sbanik1/UHV-Chamber-Designs/6 Way Cross Setup/6 way cross setup.SLDASM

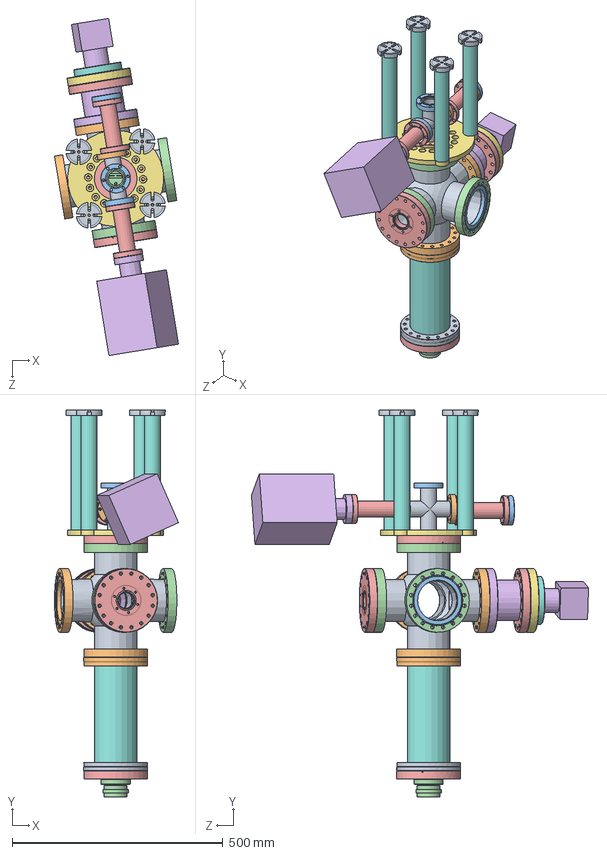
[picture p22: CAD file, 2020-12-12]
6 Way Cross Setup/6 way cross setup.SLDASM
294.7 x 919.1 x 800.7 mm
110026 (6.0 X 4.0 NR) x 3
100026 (6.0 X 4.0 INS) x 3
100026 (6.0 X 4.0 REC) x 3
6WayPump outer
6WayPump inner
6WayPump conflat
405002 P1_405002-001 x 2
405002 P2_110014 (2.75 X 1.5 NR)_1 x 2
405002 P4_100014 (2.75 X 1.5 REC)_1 x 2
405002 P5_100014 (2.75 X 1.5 INS)_1 x 2
402002 rev A x 2
RGAevision2
Washer 6 Way Cross
P0001632
P0000235
P0000448
P0000507
Varian Tisub
NexTorr Nipple P1_110025 modified
NexTorr Nipple P2_110025 modified
NexTorr Nipple Reducer_150018
Damped Post for 6 way cross P1 x 4
Damped Post for 6 way cross P3_PB2 x 4
Damped Post for 6 way cross P2_90322A235 x 8
Ion Gauge conflat_110008_1
Ion Gauge Inner Filaments
