sbanik1/UHV-Chamber-Designs/Main Chamber/Bucket Window/Bucket Window.SLDASM

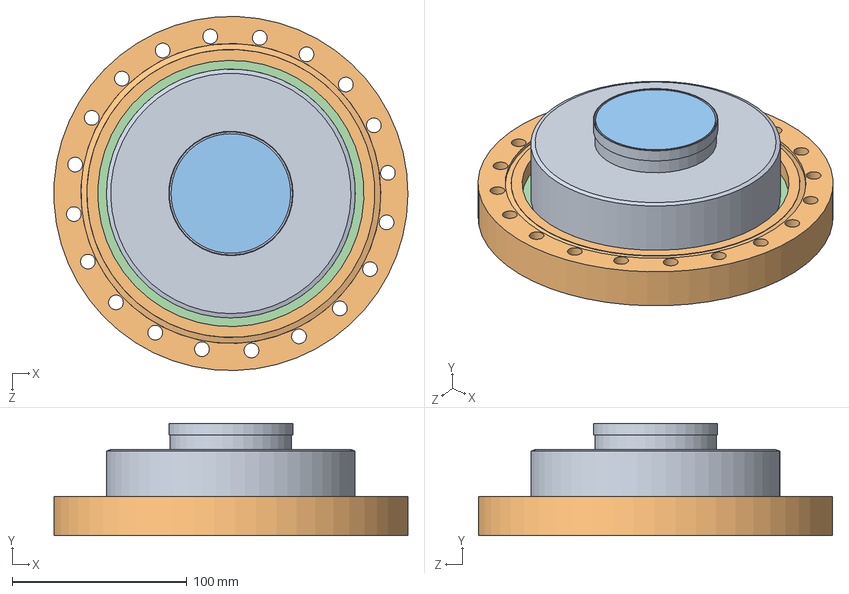
[picture p23: CAD file, 2020-12-12]
Main Chamber/Bucket Window/Bucket Window.SLDASM
202.3 x 64.0 x 202.3 mm
ISAdaptor
ISFlange
ISWindow
RecessedRing
