sbanik1/UHV-Chamber-Designs/Main Chamber/Mini lens stack holder/1.33 Viewport/1.33 Viewport.SLDASM

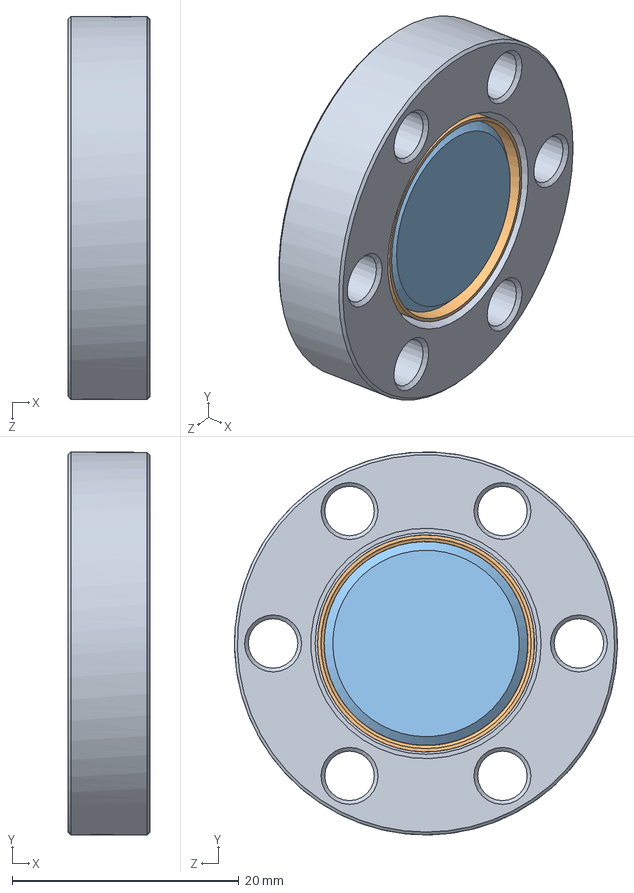
[picture p24: CAD file, 2020-12-12]
Main Chamber/Mini lens stack holder/1.33 Viewport/1.33 Viewport.SLDASM
7.24 x 33.8 x 33.8 mm
0784101L
0194307B
1002201A
