sbanik1/UHV-Chamber-Designs/2D MOT/Conical Adapter 1.33-2.75/Conical Adapter 1.33-2.75.SLDASM

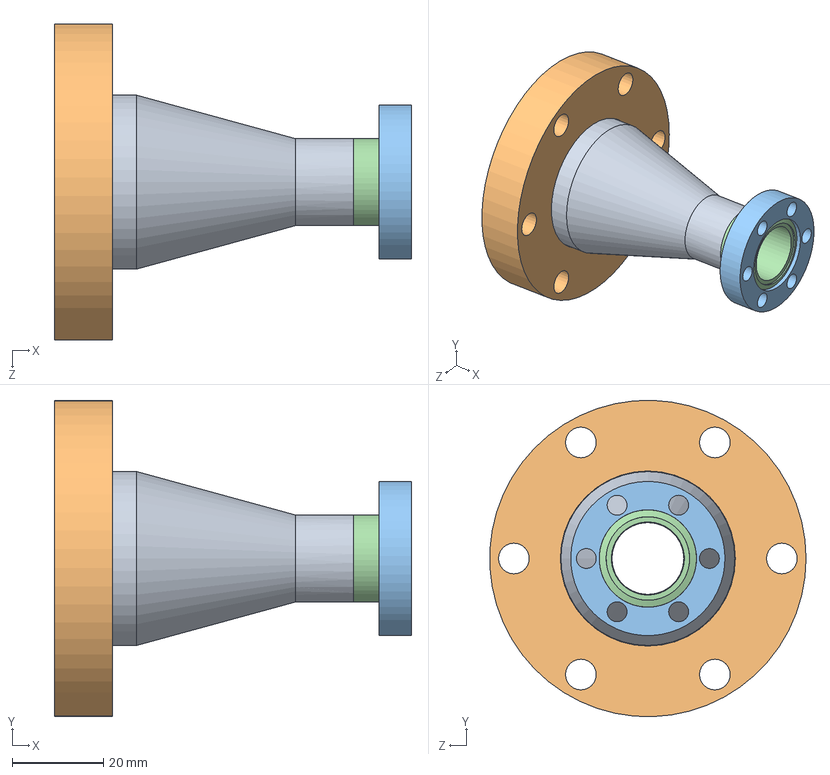
[picture p25: CAD file, 2020-12-12]
2D MOT/Conical Adapter 1.33-2.75/Conical Adapter 1.33-2.75.SLDASM
78.2 x 69.3 x 69.3 mm
110014 (2.75 X 1.5 NR)
100004 (1.33 X .75 REC)
100004 (1.33 X .75 INS)
