sbanik1/UHV-Chamber-Designs/2D MOT/Tenway Cross/Second Species Assembly.SLDASM

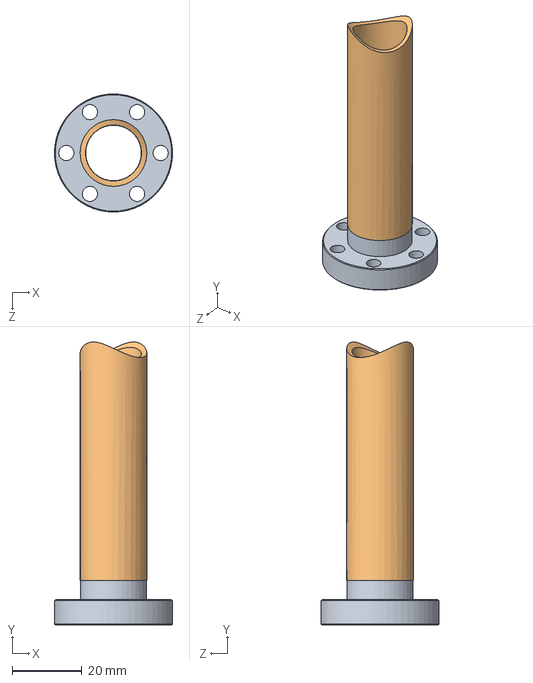
[picture p26: CAD file, 2020-12-12]
2D MOT/Tenway Cross/Second Species Assembly.SLDASM
33.8 x 80.9 x 33.8 mm
MiniFlange-weld-mine
OvenTube
