sbanik1/UHV-Chamber-Designs/6 Way Cross Setup/Damped posts/Damped Post for 6 way cross.SLDASM

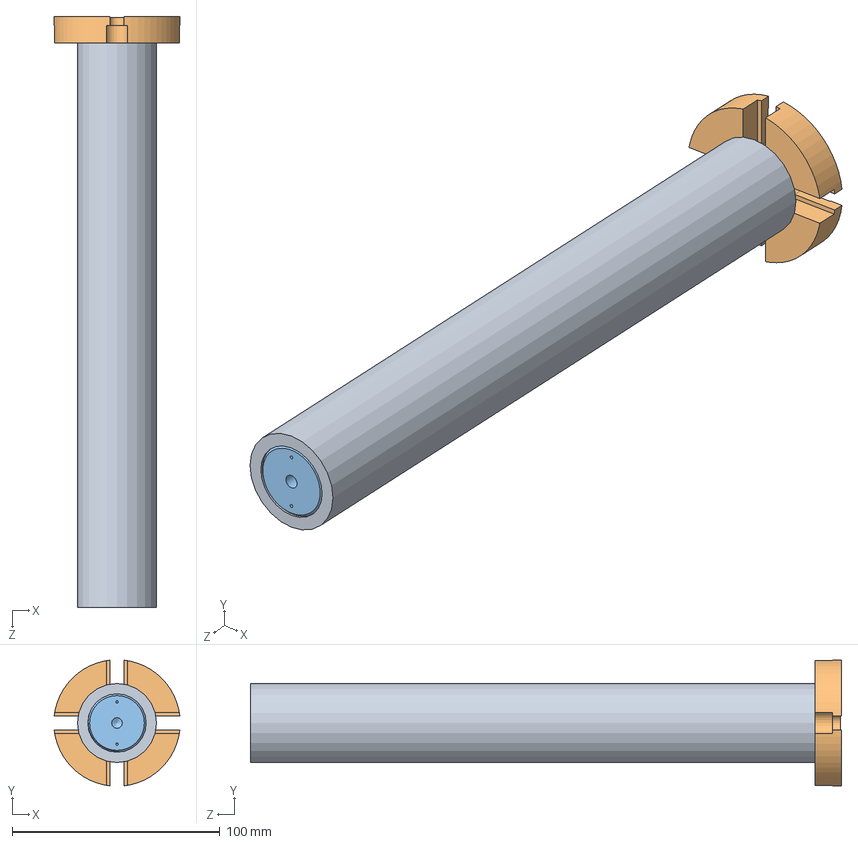
[picture p27: CAD file, 2020-12-12]
6 Way Cross Setup/Damped posts/Damped Post for 6 way cross.SLDASM
60.6 x 60.6 x 284.8 mm
Damped Post for 6 way cross P1
Damped Post for 6 way cross P3_PB2
Damped Post for 6 way cross P2_90322A235 x 2
