sbanik1/UHV-Chamber-Designs/Main Chamber/Damped Post Main Chamber/Damped Post for Main Chamber Bottom.SLDASM

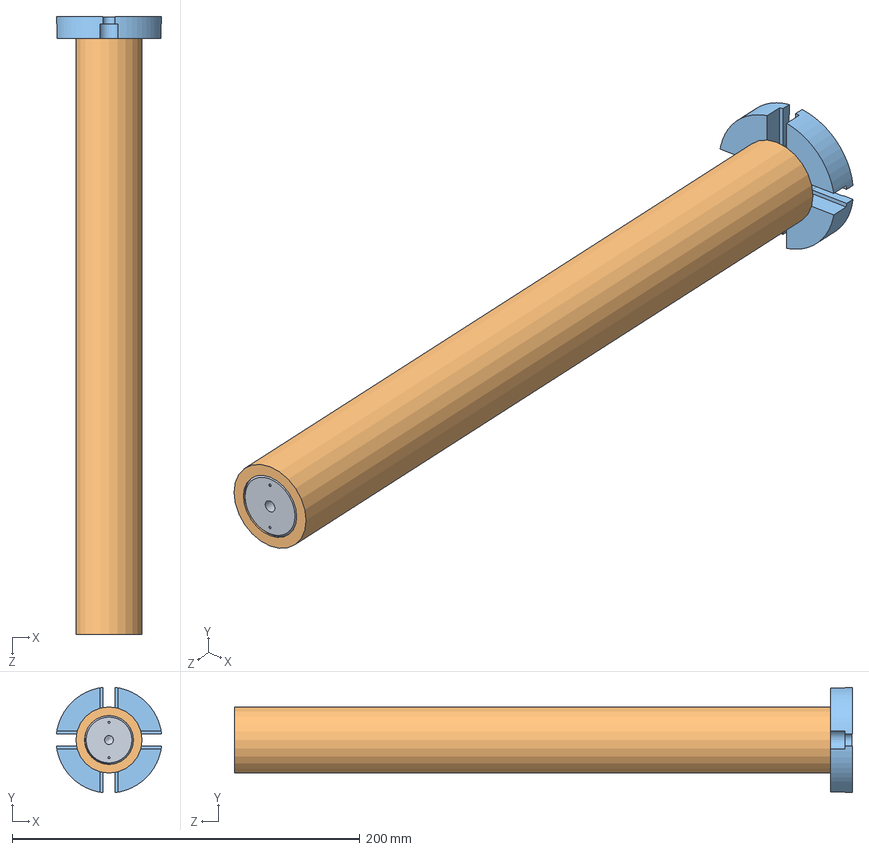
[picture p28: CAD file, 2020-12-12]
Main Chamber/Damped Post Main Chamber/Damped Post for Main Chamber Bottom.SLDASM
60.6 x 60.6 x 355.6 mm
Damped Post for Main Chamber P2_90322A235 x 2
Damped Post for Main Chamber Bottom P1
Damped Post for Main Chamber P3_PB2
