sbanik1/UHV-Chamber-Designs/2D MOT/Erbium Source/Er Source P1.SLDASM

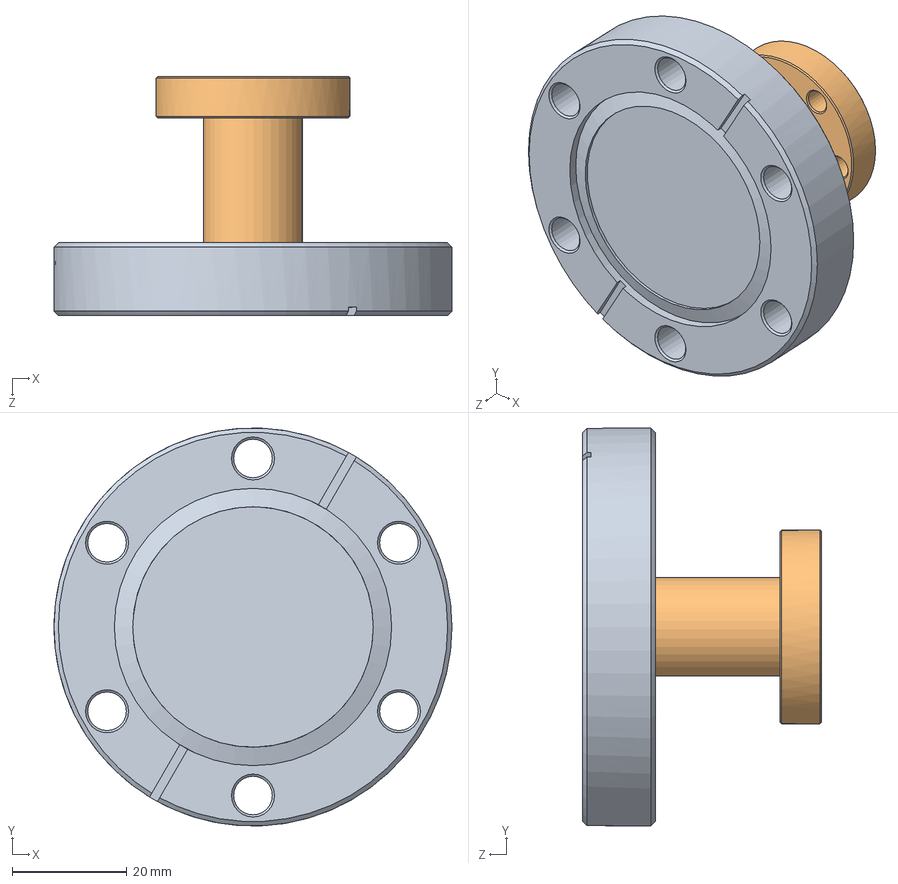
[picture p29: CAD file, 2020-12-12]
2D MOT/Erbium Source/Er Source P1.SLDASM
69.3 x 69.3 x 41.7 mm
Er Source P1-2_110008
Er Source P1-1_110002
