sbanik1/UHV-Chamber-Designs/6 Way Cross Setup/Ion Gauge/Ion Gauge.SLDASM

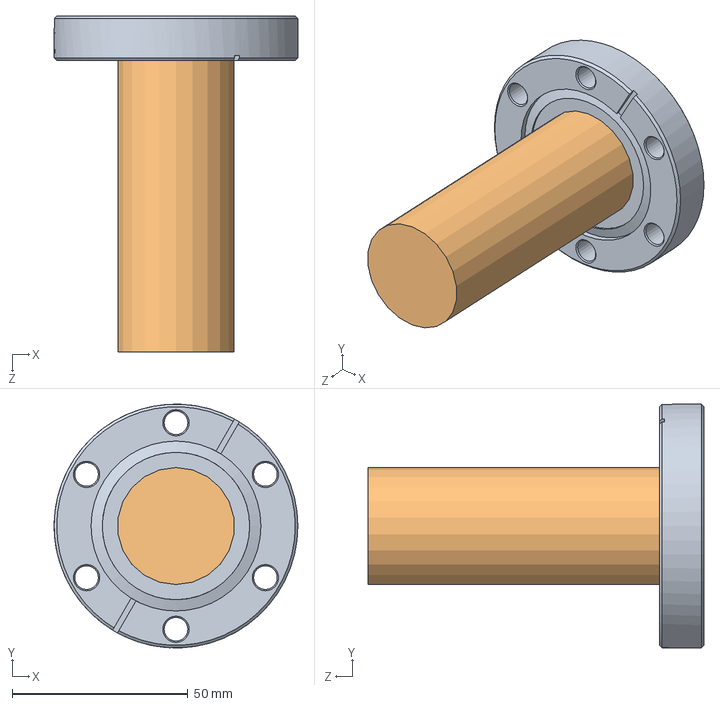
[picture p30: CAD file, 2020-12-12]
6 Way Cross Setup/Ion Gauge/Ion Gauge.SLDASM
69.3 x 69.3 x 95.6 mm
Ion Gauge conflat_110008_1
Ion Gauge Inner Filaments
