sbanik1/UHV-Chamber-Designs/6 Way Cross Setup/NextTorr Nipple/NexTorr Nipple.SLDASM

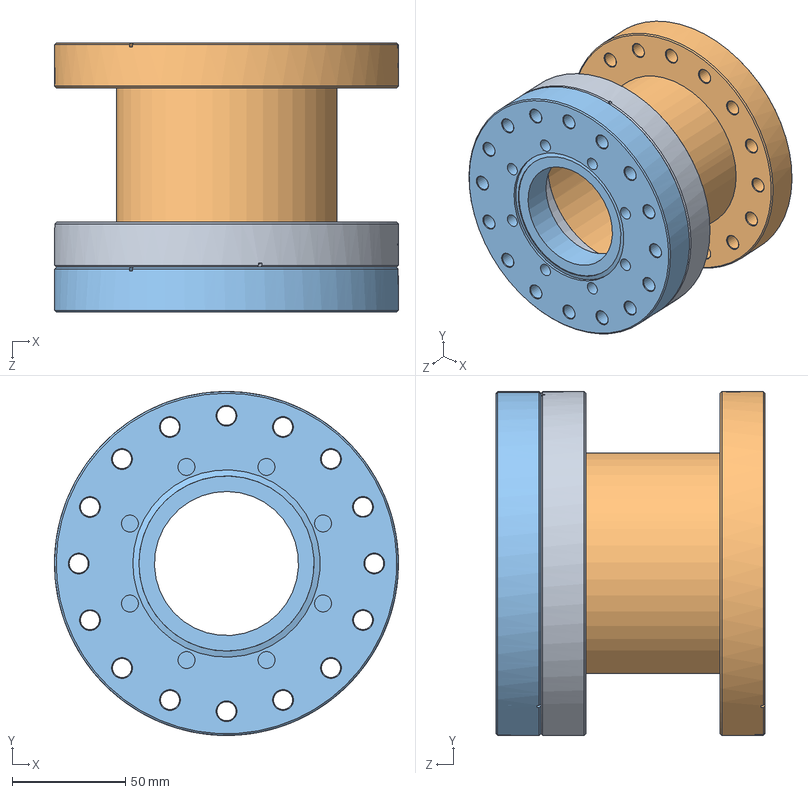
[picture p31: CAD file, 2020-12-12]
6 Way Cross Setup/NextTorr Nipple/NexTorr Nipple.SLDASM
151.6 x 151.6 x 118.6 mm
NexTorr Nipple P1_110025 modified
NexTorr Nipple P2_110025 modified
NexTorr Nipple Reducer_150018
