sbanik1/UHV-Chamber-Designs/6 Way Cross Setup/TSP Nipple/TSP nipple_fn-0600.SLDASM

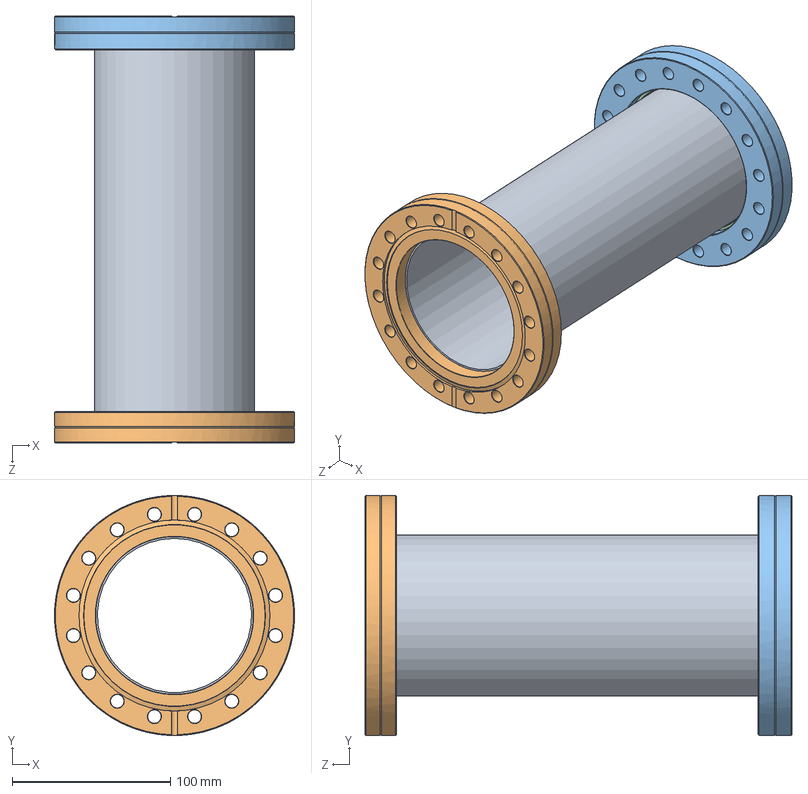
[picture p32: CAD file, 2020-12-12]
6 Way Cross Setup/TSP Nipple/TSP nipple_fn-0600.SLDASM
151.6 x 151.6 x 269.7 mm
P0001632
P0000235
P0000448
P0000507
