sbanik1/UHV-Chamber-Designs/Main Chamber/4.5 VP Assembly/4.5 Viewport/Viewport 4.5_9722007.SLDASM

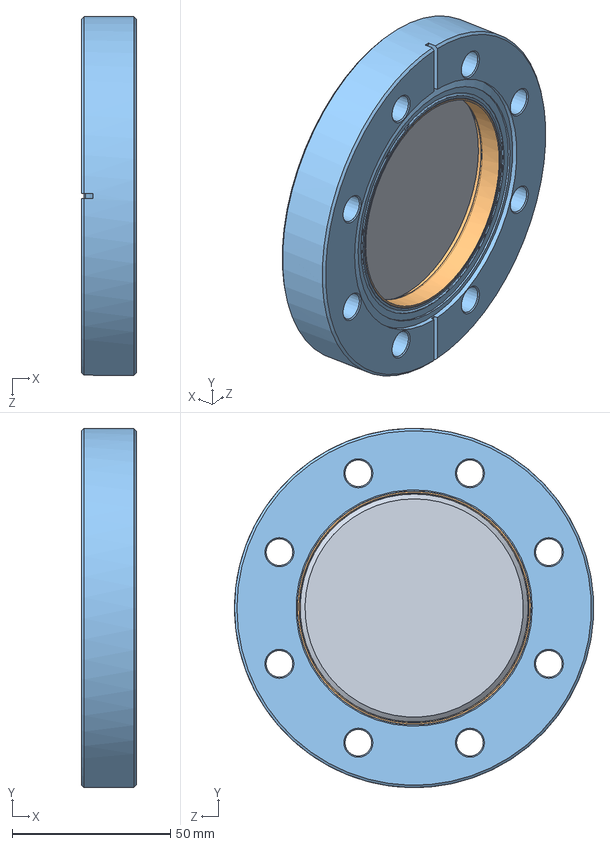
[picture p33: CAD file, 2020-12-12]
Main Chamber/4.5 VP Assembly/4.5 Viewport/Viewport 4.5_9722007.SLDASM
17.3 x 113.5 x 113.4 mm
1002203A
Viewport 4.5 P1_0194302B
Viewport 4.5 P2_0194603B
