sbanik1/UHV-Chamber-Designs/Main Chamber/Damped Post Main Chamber/Damped Post for Main Chamber Bottom P1.SLDPRT

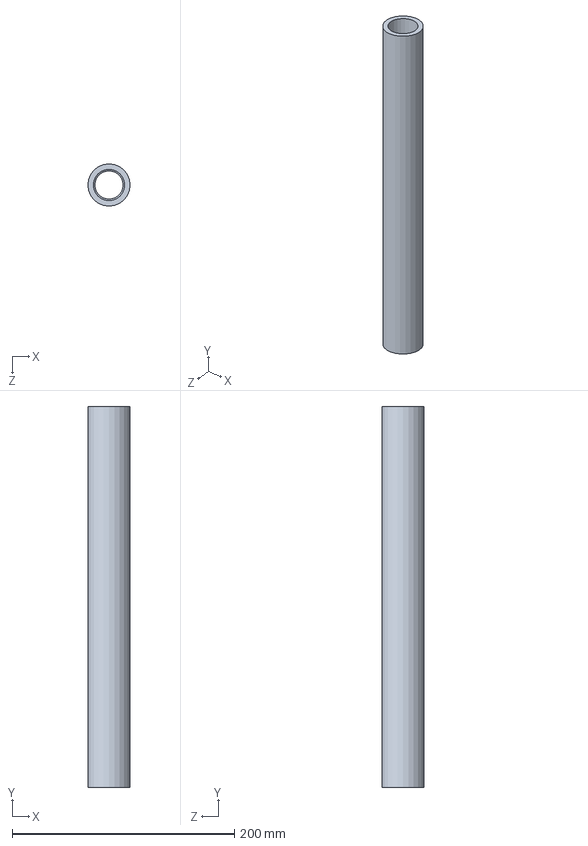
[picture p34: CAD file, 2020-12-12]
Main Chamber/Damped Post Main Chamber/Damped Post for Main Chamber Bottom P1.SLDPRT
38.1 x 342.9 x 38.1 mm
