sbanik1/UHV-Chamber-Designs/2D MOT/2.75 Four Way Cross/2.75 Four Way Cross.SLDASM

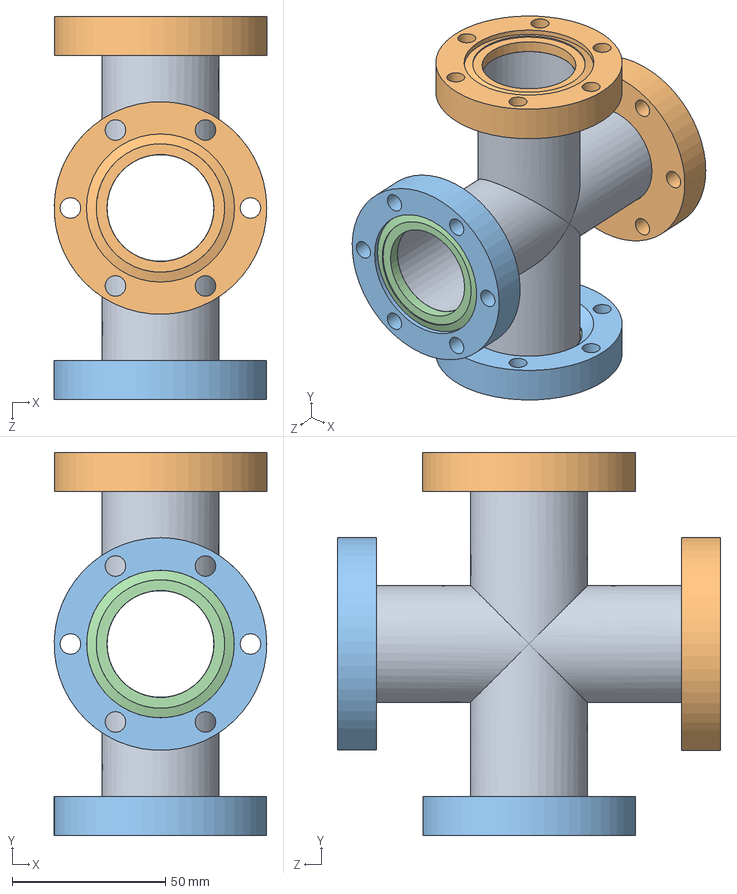
[picture p35: CAD file, 2020-12-12]
2D MOT/2.75 Four Way Cross/2.75 Four Way Cross.SLDASM
69.3 x 124.9 x 124.9 mm
405002 P1_405002-001 x 2
405002 P2_110014 (2.75 X 1.5 NR)_1 x 2
405002 P4_100014 (2.75 X 1.5 REC)_1 x 2
405002 P5_100014 (2.75 X 1.5 INS)_1 x 2
