sbanik1/UHV-Chamber-Designs/2D MOT/2.75 Window/2.75 Window.SLDASM

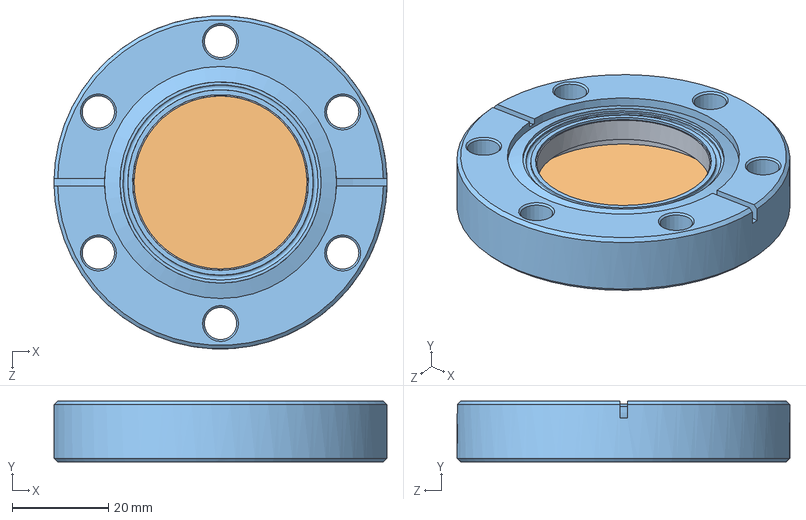
[picture p36: CAD file, 2020-12-12]
2D MOT/2.75 Window/2.75 Window.SLDASM
69.3 x 12.7 x 69.3 mm
2.75 Window P1-1
2.75 Window P1-2
2.75 Window P2
