sbanik1/UHV-Chamber-Designs/Main Chamber/Damped Post Main Chamber/Damped Post for Main Chamber P2_90322A235.SLDPRT

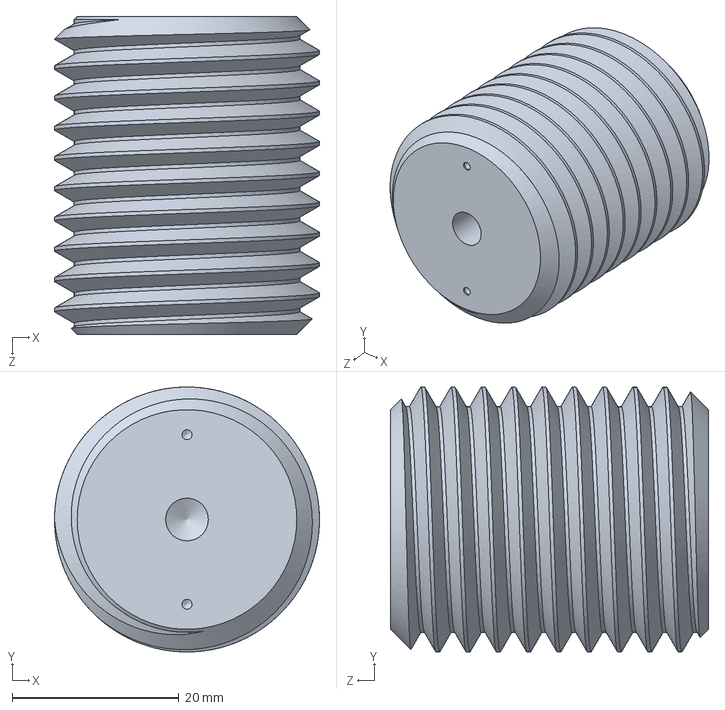
[picture p37: CAD file, 2020-12-12]
Main Chamber/Damped Post Main Chamber/Damped Post for Main Chamber P2_90322A235.SLDPRT
31.7 x 31.7 x 38.1 mm
