sbanik1/UHV-Chamber-Designs/2D MOT/Tenway Cross/Chamber Tube Assembly.SLDASM

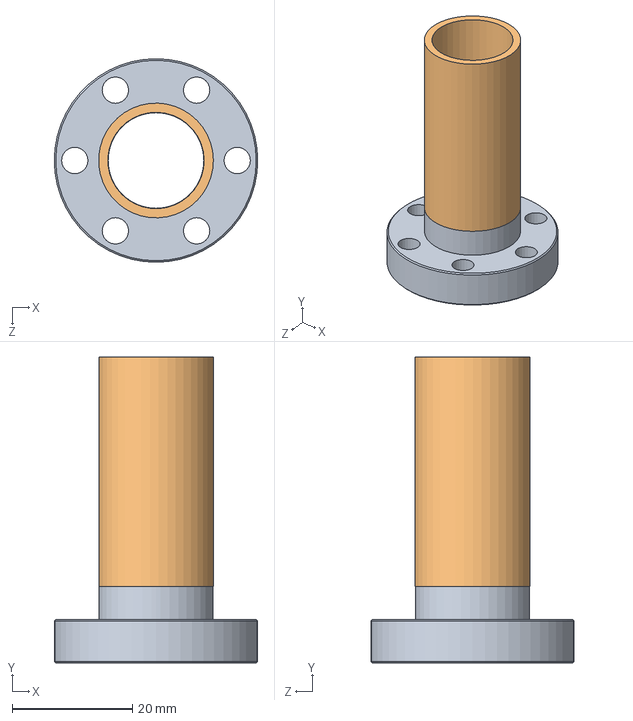
[picture p38: CAD file, 2020-12-12]
2D MOT/Tenway Cross/Chamber Tube Assembly.SLDASM
33.8 x 50.8 x 33.8 mm
MiniFlange-weld-mine
ChamberTube
