sbanik1/UHV-Chamber-Designs/Main Chamber/Damped Post Main Chamber/Damped Post for Main Chamber P3_PB2.sldprt

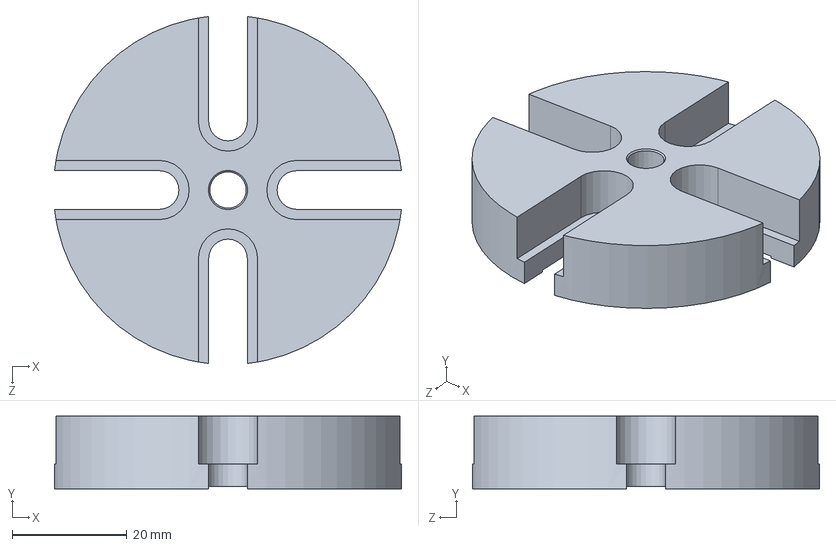
[picture p39: CAD file, 2020-12-12]
Main Chamber/Damped Post Main Chamber/Damped Post for Main Chamber P3_PB2.sldprt
60.6 x 12.7 x 60.6 mm
