sbanik1/UHV-Chamber-Designs/2D MOT/2.75 Window/2.75 Window P1.SLDASM

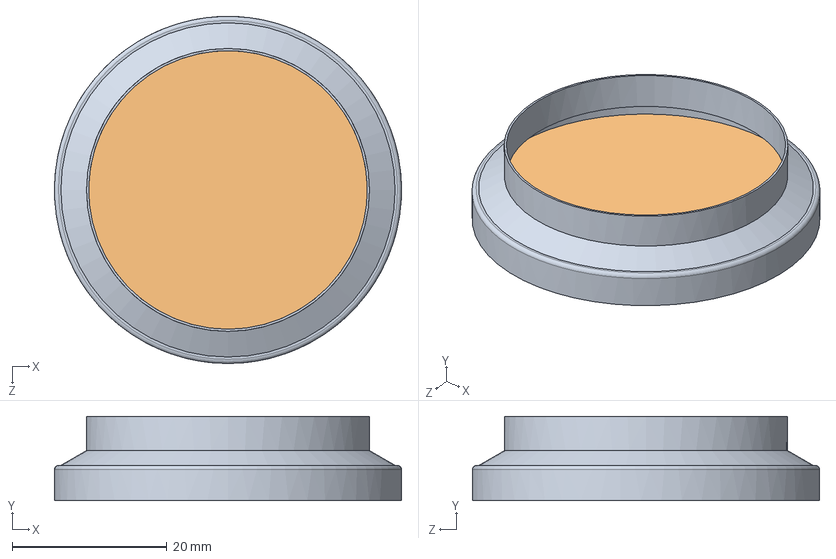
[picture p40: CAD file, 2020-12-12]
2D MOT/2.75 Window/2.75 Window P1.SLDASM
44.9 x 10.9 x 44.9 mm
2.75 Window P1-1
2.75 Window P1-2
