sbanik1/UHV-Chamber-Designs/2D MOT/Erbium Source/Er Source.SLDASM

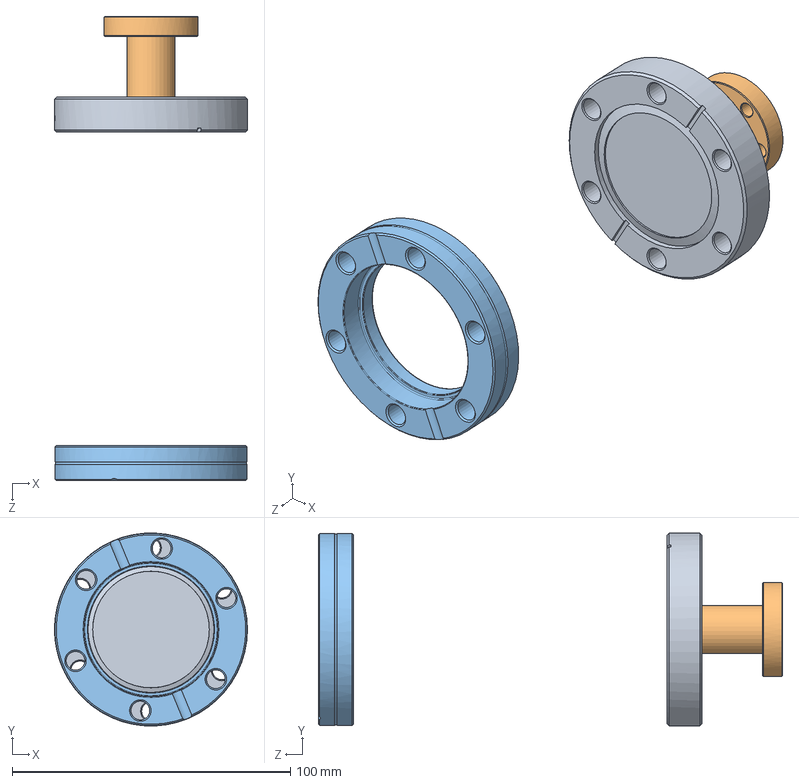
[picture p41: CAD file, 2020-12-12]
2D MOT/Erbium Source/Er Source.SLDASM
69.3 x 69.3 x 166.9 mm
Er Source P1-2_110008
Er Source P1-1_110002
Er Source P2-1-1_P0000436
