sbanik1/UHV-Chamber-Designs/Main Chamber/Damped Post Main Chamber/Damped Post Main Chamber_DP14A.sldprt

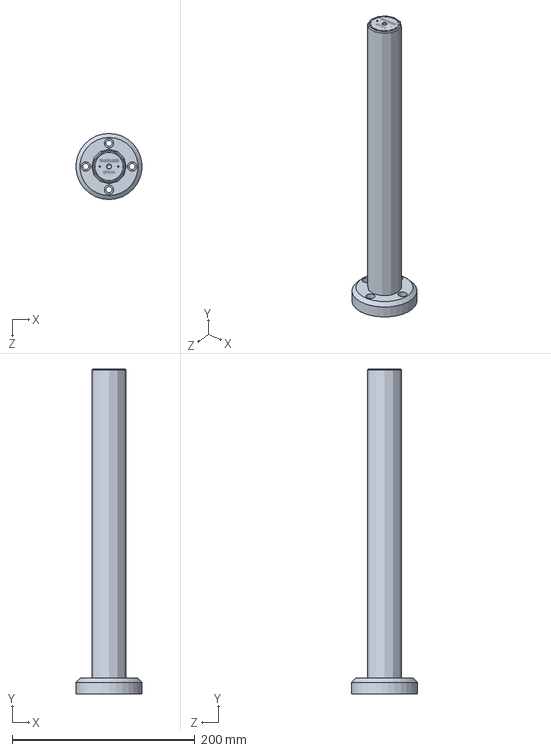
[picture p42: CAD file, 2020-12-12]
Main Chamber/Damped Post Main Chamber/Damped Post Main Chamber_DP14A.sldprt
72.0 x 355.6 x 72.4 mm
