sbanik1/UHV-Chamber-Designs/2D MOT/Tenway Cross/TenwayCross.SLDASM

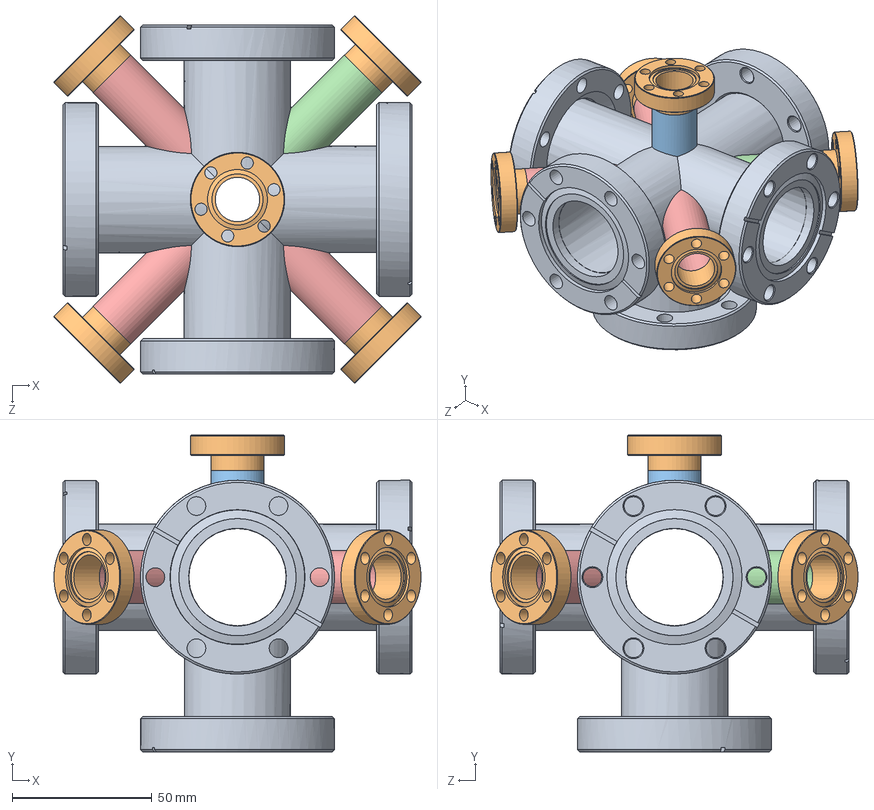
[picture p43: CAD file, 2020-12-12]
2D MOT/Tenway Cross/TenwayCross.SLDASM
131.3 x 113.3 x 131.3 mm
5way MDC-406002-mine
MiniFlange-weld-mine x 5
ChamberTube
CameraTube
OvenTube x 3
