sbanik1/UHV-Chamber-Designs/2D MOT/2.75 Nipple_402002 rev A/2D MOT nipple_402002 rev A.SLDPRT

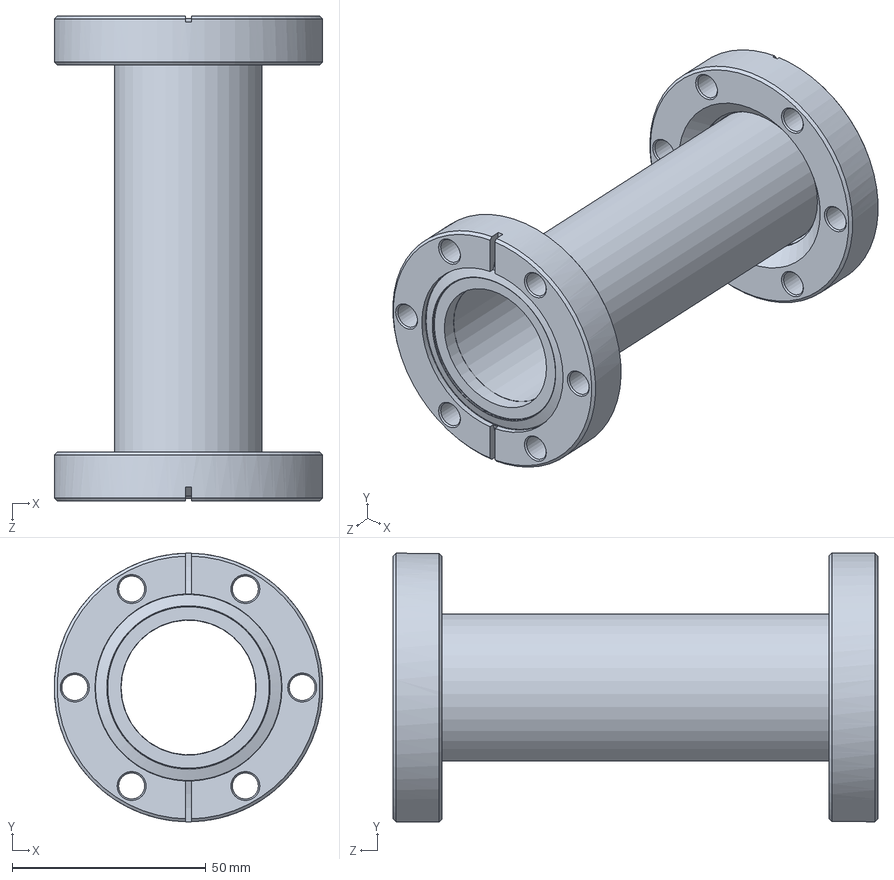
[picture p44: CAD file, 2020-12-12]
2D MOT/2.75 Nipple_402002 rev A/2D MOT nipple_402002 rev A.SLDPRT
69.3 x 69.3 x 125.2 mm
