sbanik1/UHV-Chamber-Designs/2D MOT/2DMOT Bias Coils/Coil mount.SLDPRT

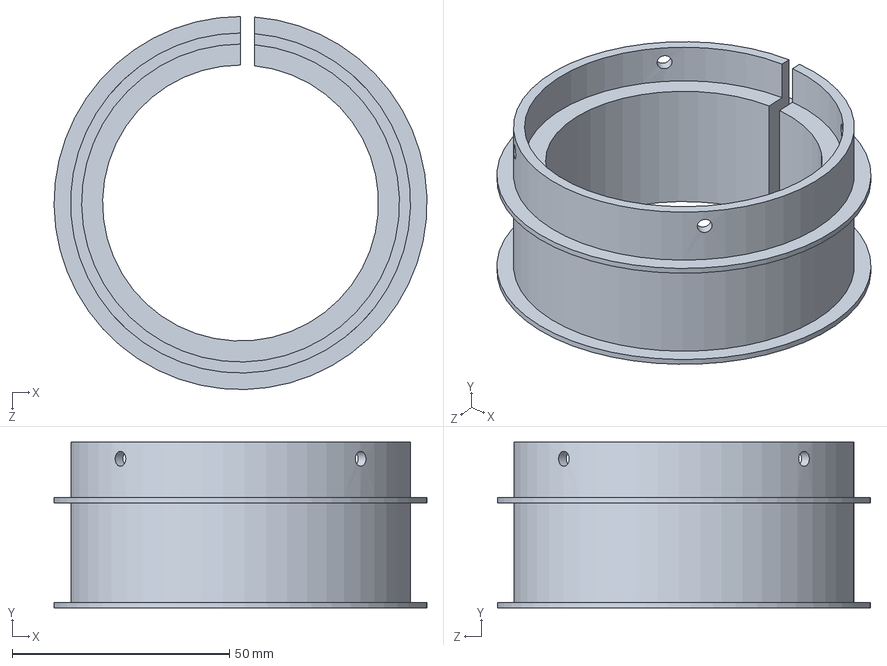
[picture p45: CAD file, 2020-12-12]
2D MOT/2DMOT Bias Coils/Coil mount.SLDPRT
85.8 x 38.1 x 85.8 mm
