sbanik1/UHV-Chamber-Designs/2D MOT/Angle Valve/Angle Valve_314003.SLDPRT

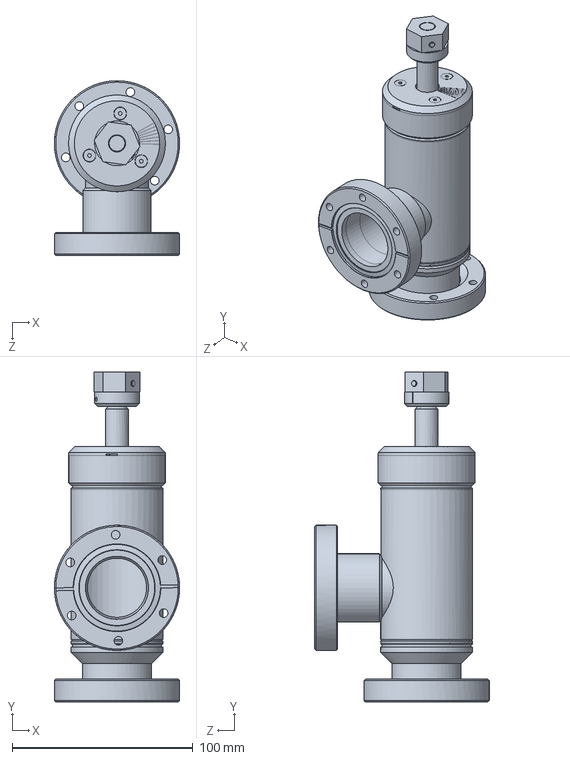
[picture p46: CAD file, 2020-12-12]
2D MOT/Angle Valve/Angle Valve_314003.SLDPRT
69.3 x 182.7 x 96.6 mm
