sbanik1/UHV-Chamber-Designs/2D MOT/Differential Pumping Tube/DiffPumpTube.SLDPRT

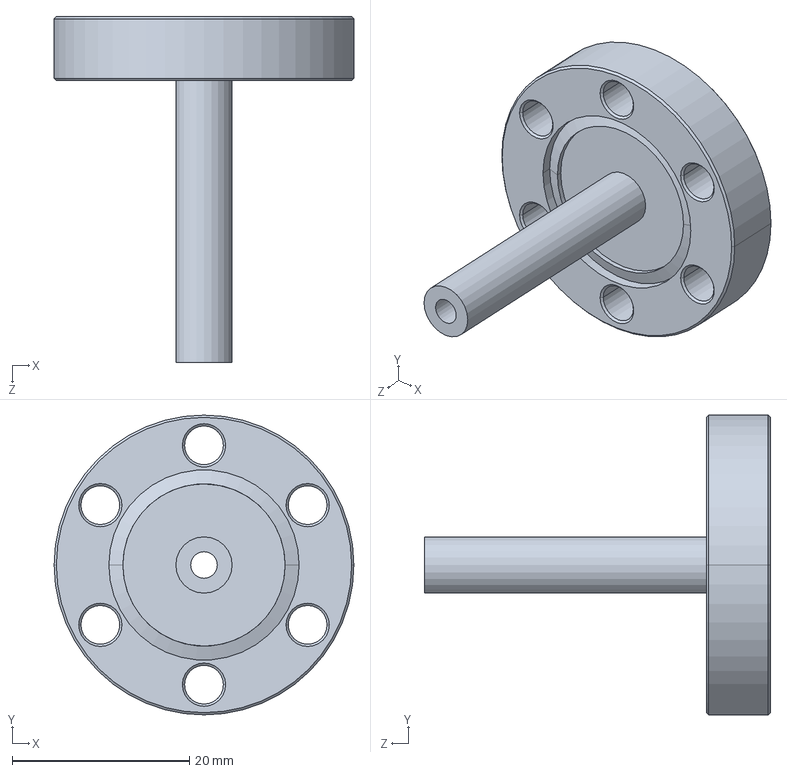
[picture p48: CAD file, 2021-06-03]
2D MOT/Differential Pumping Tube/DiffPumpTube.SLDPRT
33.8 x 33.8 x 39.0 mm
