sbanik1/UHV-Chamber-Designs/2D MOT/Gate Valve/Gate Valve 302000.SLDPRT

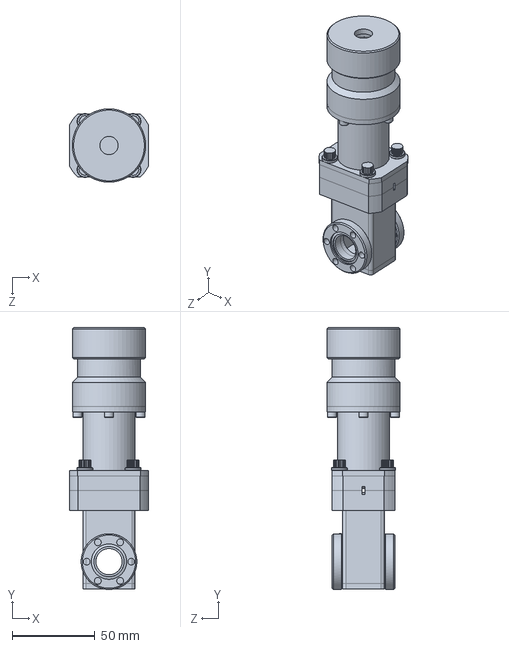
[picture p49: CAD file, 2020-12-12]
2D MOT/Gate Valve/Gate Valve 302000.SLDPRT
47.6 x 158.8 x 44.5 mm
