sbanik1/UHV-Chamber-Designs/6 Way Cross Setup/6 Way Cross Getter SAES D-500/6WayPump conflat.SLDPRT

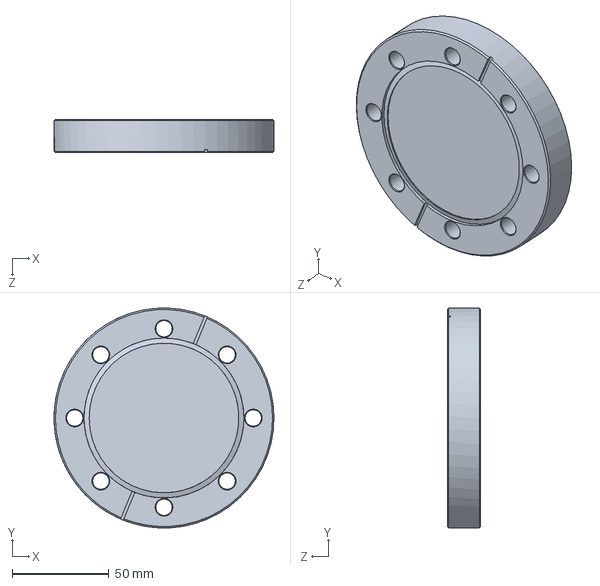
[picture p50: CAD file, 2020-12-12]
6 Way Cross Setup/6 Way Cross Getter SAES D-500/6WayPump conflat.SLDPRT
113.5 x 113.5 x 17.3 mm
