sbanik1/UHV-Chamber-Designs/6 Way Cross Setup/Baffle.SLDPRT

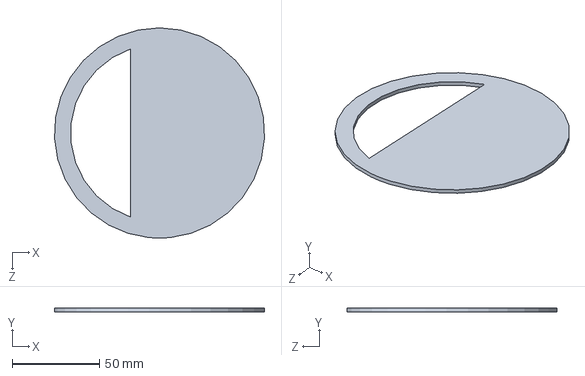
[picture p51: CAD file, 2020-12-12]
6 Way Cross Setup/Baffle.SLDPRT
120.2 x 2.03 x 120.4 mm
