sbanik1/UHV-Chamber-Designs/6 Way Cross Setup/Ion Gauge/Ion Gauge conflat_110008_1.SLDPRT

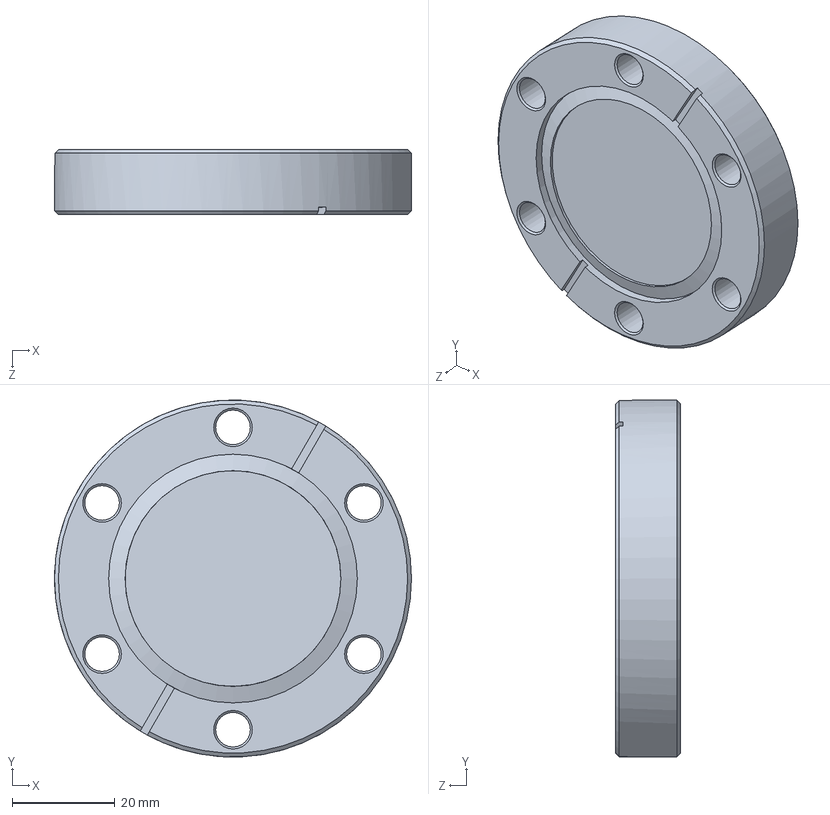
[picture p52: CAD file, 2020-12-12]
6 Way Cross Setup/Ion Gauge/Ion Gauge conflat_110008_1.SLDPRT
69.3 x 69.3 x 12.7 mm
