sbanik1/UHV-Chamber-Designs/6 Way Cross Setup/RGA/RGAevision2.SLDPRT

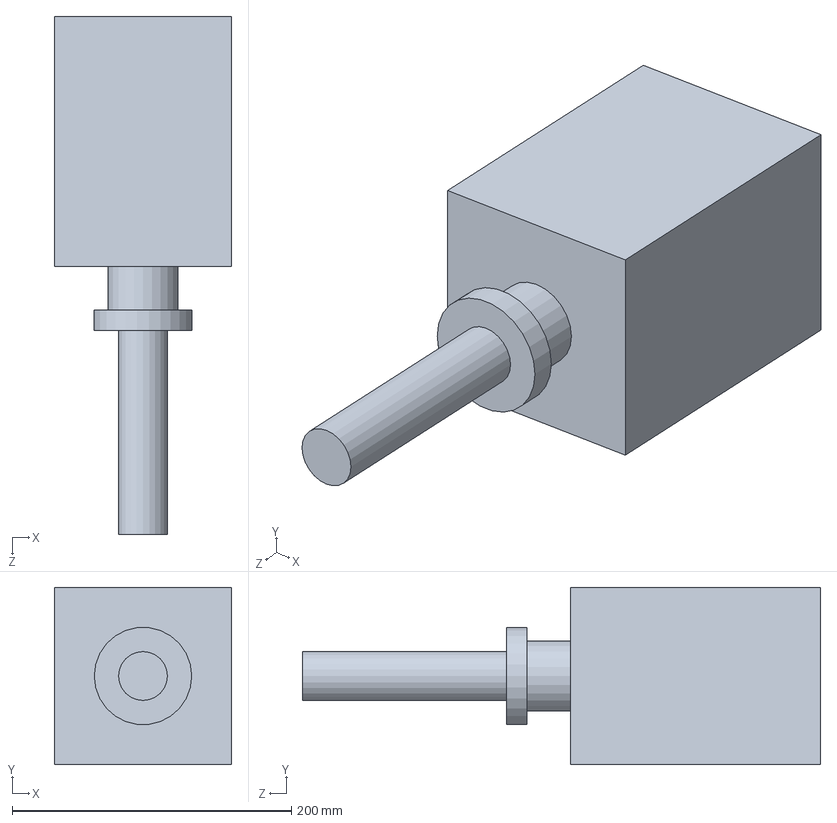
[picture p54: CAD file, 2020-12-12]
6 Way Cross Setup/RGA/RGAevision2.SLDPRT
127.0 x 127.0 x 371.1 mm
