sbanik1/UHV-Chamber-Designs/6 Way Cross Setup/Ti Sub/Varian Tisub.SLDPRT

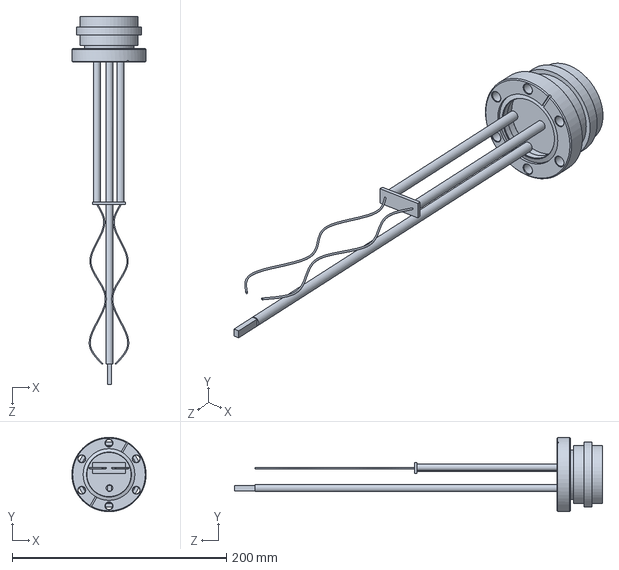
[picture p55: CAD file, 2020-12-12]
6 Way Cross Setup/Ti Sub/Varian Tisub.SLDPRT
69.3 x 69.3 x 343.6 mm
