sbanik1/UHV-Chamber-Designs/Main Chamber/Bucket Window/RecessedRing.SLDPRT

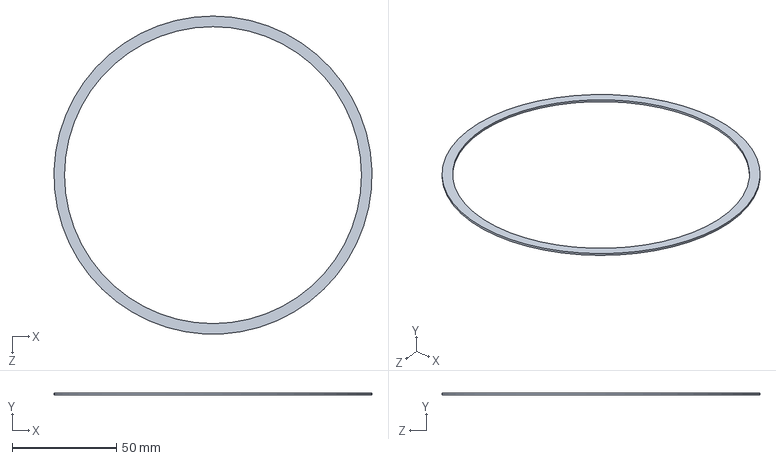
[picture p57: CAD file, 2020-12-12]
Main Chamber/Bucket Window/RecessedRing.SLDPRT
152.3 x 1 x 152.3 mm
