sbanik1/UHV-Chamber-Designs/Main Chamber/Chamber/Modified Kimball Chamber.SLDPRT

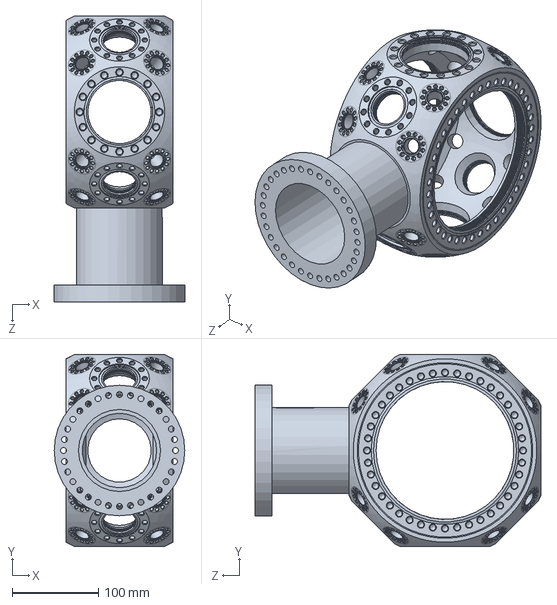
[picture p58: CAD file, 2020-12-12]
Main Chamber/Chamber/Modified Kimball Chamber.SLDPRT
151.6 x 223.0 x 332.2 mm
