sbanik1/UHV-Chamber-Designs/Optical Table Surface/optical table Surface.SLDPRT

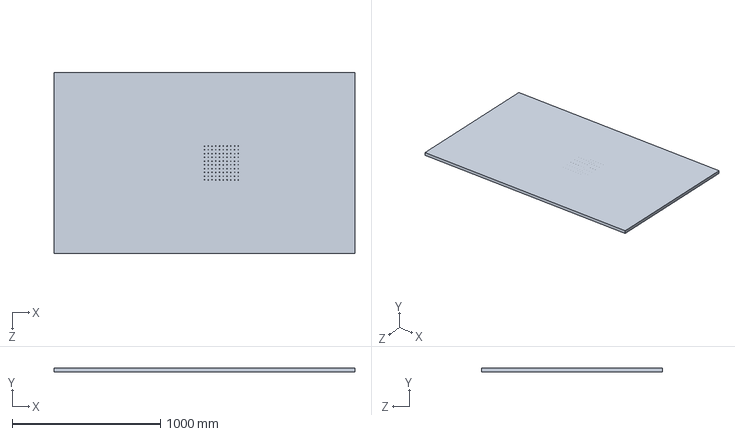
[picture p59: CAD file, 2020-12-12]
Optical Table Surface/optical table Surface.SLDPRT
2032.0 x 25.4 x 1219.2 mm
