sbanik1/UHV-Chamber-Designs/2D MOT/Sodium Oven/Cup.SLDPRT

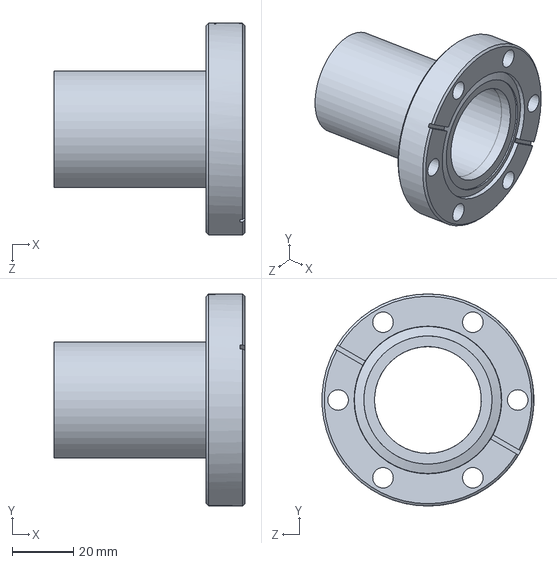
[picture p60: CAD file, 2020-12-12]
2D MOT/Sodium Oven/Cup.SLDPRT
62.5 x 69.3 x 69.3 mm
