sbanik1/UHV-Chamber-Designs/2D MOT/Tenway Cross/5way MDC-406002-mine.SLDPRT

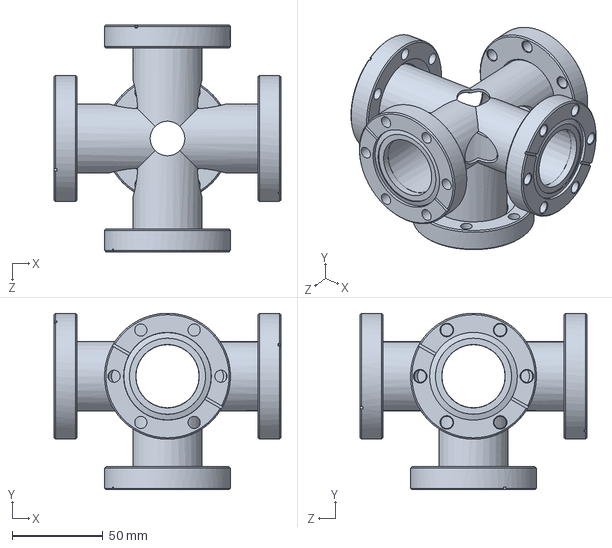
[picture p61: CAD file, 2020-12-12]
2D MOT/Tenway Cross/5way MDC-406002-mine.SLDPRT
125.0 x 97.2 x 125.0 mm
