sbanik1/UHV-Chamber-Designs/6 Way Cross Setup/NextTorr Nipple/NexTorr Nipple P2_110025 modified.SLDPRT

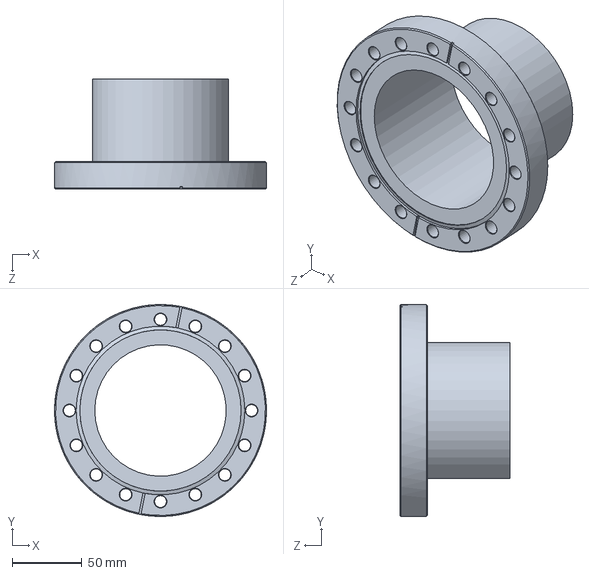
[picture p62: CAD file, 2020-12-12]
6 Way Cross Setup/NextTorr Nipple/NexTorr Nipple P2_110025 modified.SLDPRT
151.6 x 151.6 x 79.0 mm
