sbanik1/UHV-Chamber-Designs/6 Way Cross Setup/Ti Sub/TiSub 2_34CFBlankFlangeClear.SLDPRT

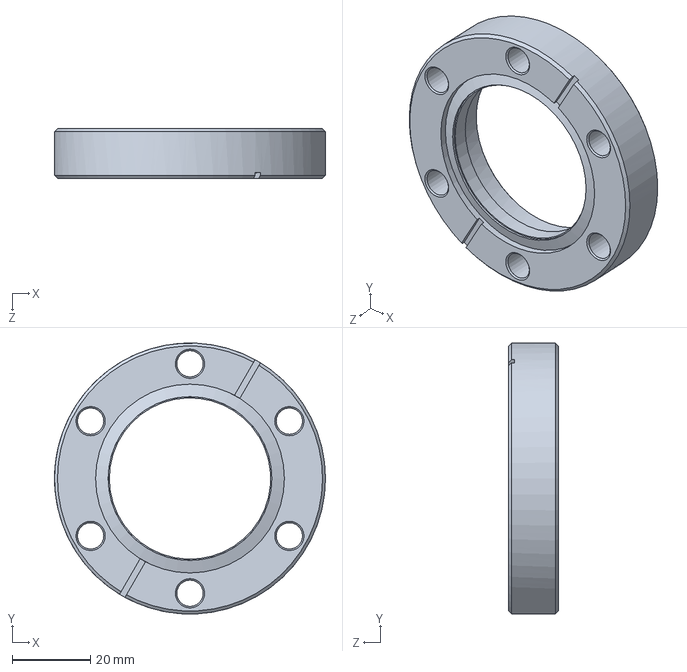
[picture p63: CAD file, 2020-12-12]
6 Way Cross Setup/Ti Sub/TiSub 2_34CFBlankFlangeClear.SLDPRT
69.3 x 69.3 x 12.7 mm
