sbanik1/UHV-Chamber-Designs/Bread Boards/Bread Board Top NO HOLES.SLDPRT

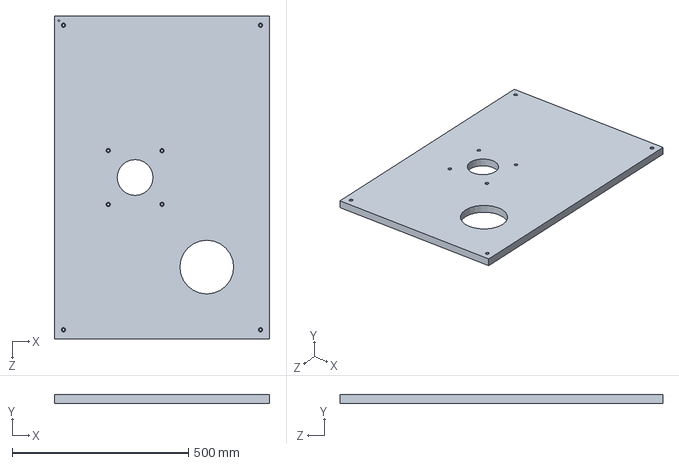
[picture p64: CAD file, 2020-12-12]
Bread Boards/Bread Board Top NO HOLES.SLDPRT
609.6 x 25.4 x 914.4 mm
