sbanik1/UHV-Chamber-Designs/Main Chamber/Damped Post Main Chamber/Chamber Top Post_P6.sldprt

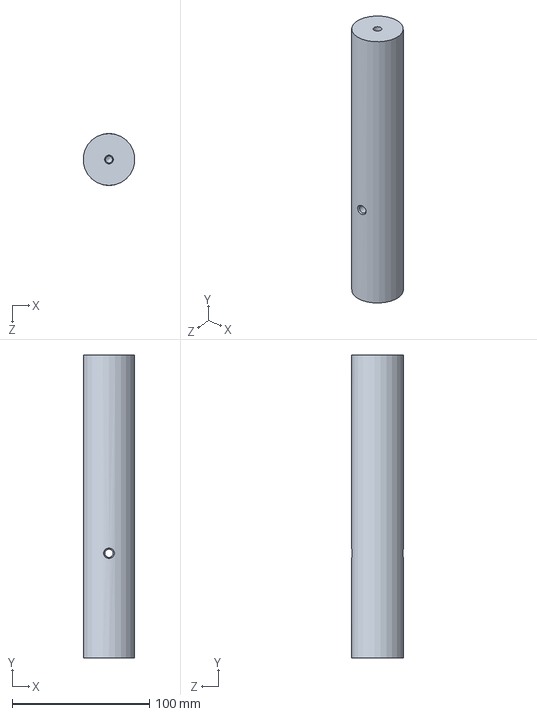
[picture p65: CAD file, 2020-12-12]
Main Chamber/Damped Post Main Chamber/Chamber Top Post_P6.sldprt
37.5 x 220.5 x 37.7 mm
