sbanik1/UHV-Chamber-Designs/2D MOT/2.75 Window/2.75 Window P1-2.SLDPRT

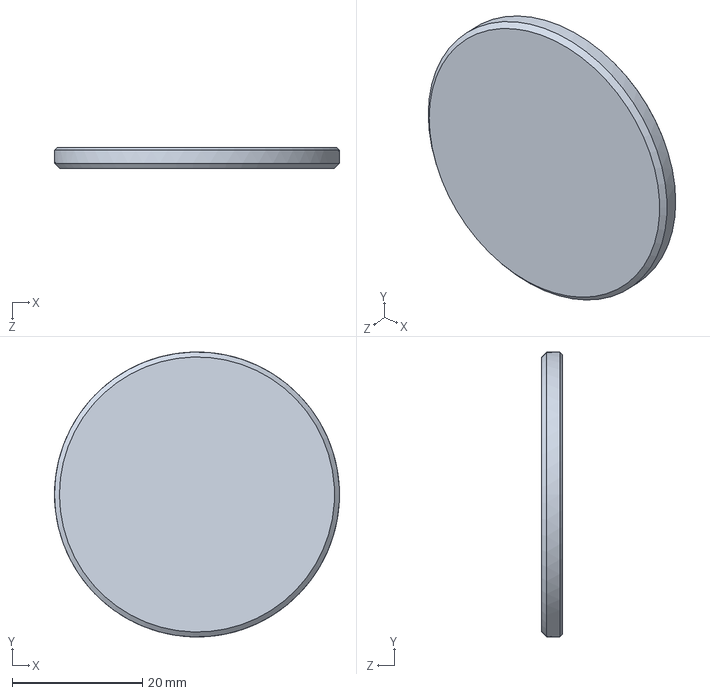
[picture p66: CAD file, 2020-12-12]
2D MOT/2.75 Window/2.75 Window P1-2.SLDPRT
43.7 x 43.7 x 3.17 mm
