sbanik1/UHV-Chamber-Designs/2D MOT/Connection nipple/Connection Nipple P2_110000.SLDPRT

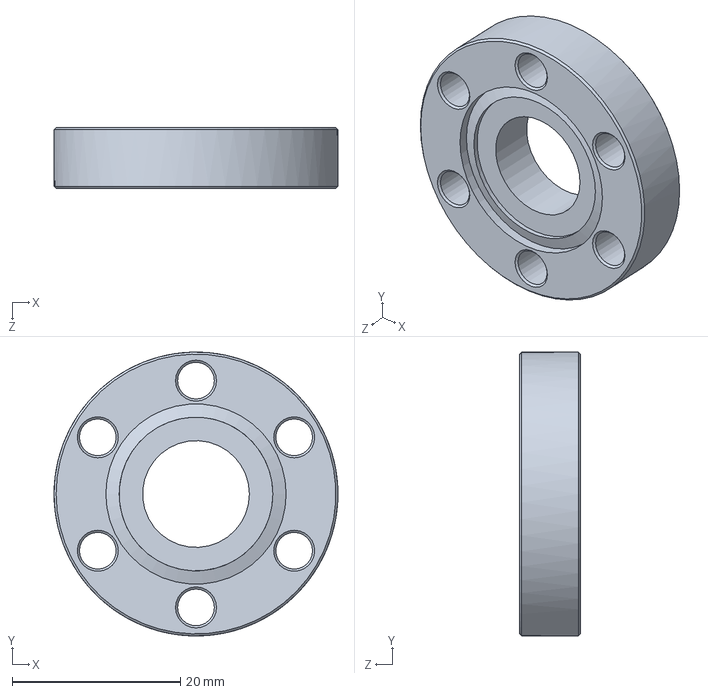
[picture p67: CAD file, 2020-12-12]
2D MOT/Connection nipple/Connection Nipple P2_110000.SLDPRT
33.8 x 33.8 x 7.24 mm
