sbanik1/UHV-Chamber-Designs/2D MOT/SAES Getter_D100-5/2D MOT Pump inner.SLDPRT

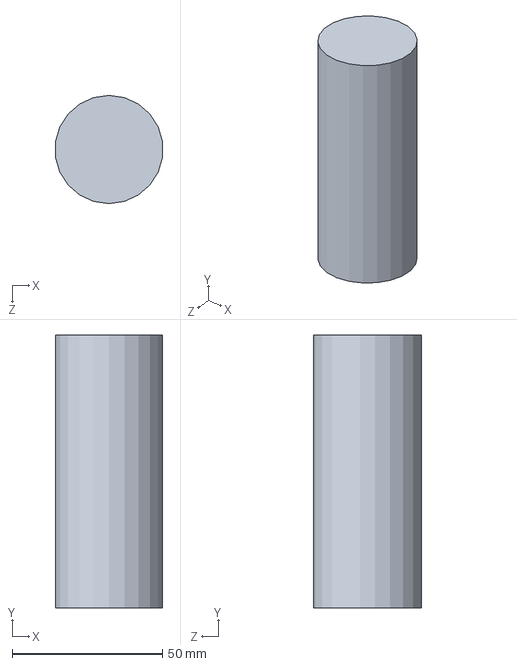
[picture p68: CAD file, 2020-12-12]
2D MOT/SAES Getter_D100-5/2D MOT Pump inner.SLDPRT
35.7 x 90.9 x 36.1 mm
