sbanik1/UHV-Chamber-Designs/6 Way Cross Setup/6 Way Cross Getter SAES D-500/6WayPump outer.SLDPRT

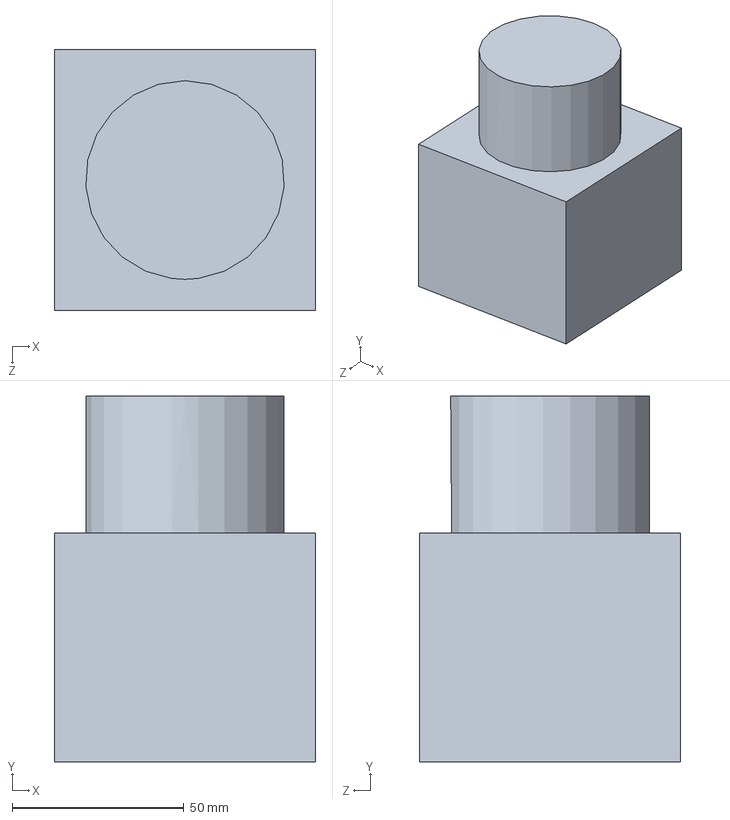
[picture p70: CAD file, 2020-12-12]
6 Way Cross Setup/6 Way Cross Getter SAES D-500/6WayPump outer.SLDPRT
76.2 x 106.7 x 76.2 mm
