sbanik1/UHV-Chamber-Designs/6 Way Cross Setup/Ion Gauge/Ion Gauge Inner Filaments.SLDPRT

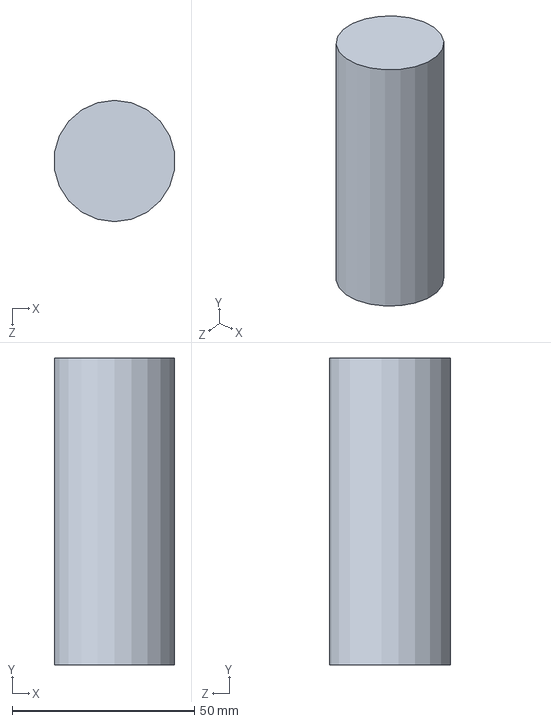
[picture p71: CAD file, 2020-12-12]
6 Way Cross Setup/Ion Gauge/Ion Gauge Inner Filaments.SLDPRT
32.9 x 84.1 x 33.3 mm
