sbanik1/UHV-Chamber-Designs/6 Way Cross Setup/NextTorr Nipple/NexTorr Nipple Reducer_150018.SLDPRT

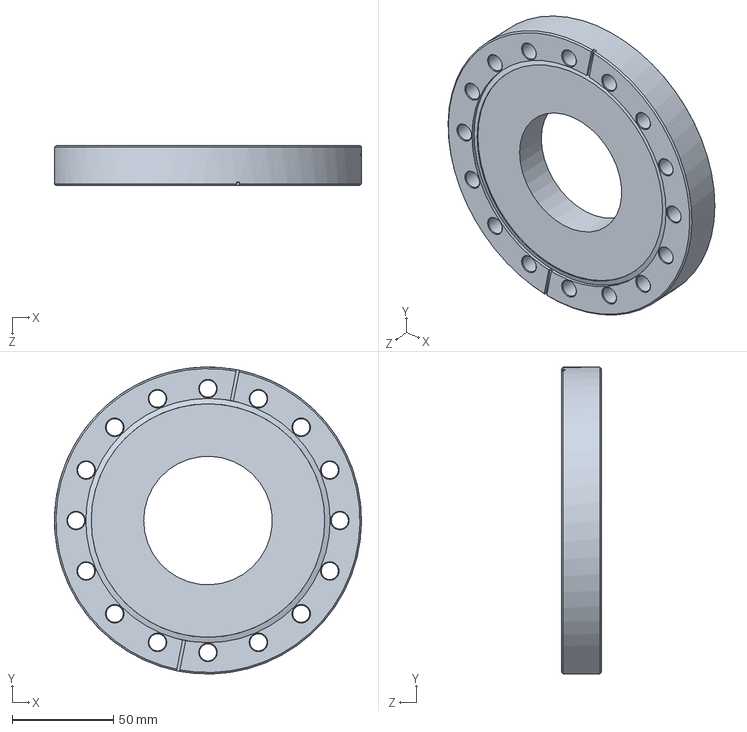
[picture p72: CAD file, 2020-12-12]
6 Way Cross Setup/NextTorr Nipple/NexTorr Nipple Reducer_150018.SLDPRT
151.6 x 151.6 x 19.8 mm
