sbanik1/UHV-Chamber-Designs/Main Chamber/Bucket Window/ISFlange.SLDPRT

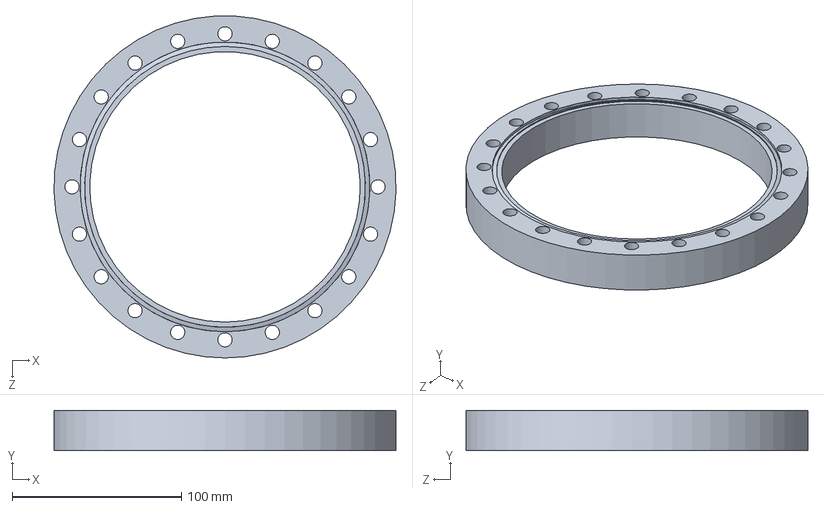
[picture p74: CAD file, 2020-12-12]
Main Chamber/Bucket Window/ISFlange.SLDPRT
202.3 x 23.9 x 202.3 mm
