sbanik1/UHV-Chamber-Designs/2D MOT/SAES Getter_D100-5/2D MOT Pump outer.SLDPRT

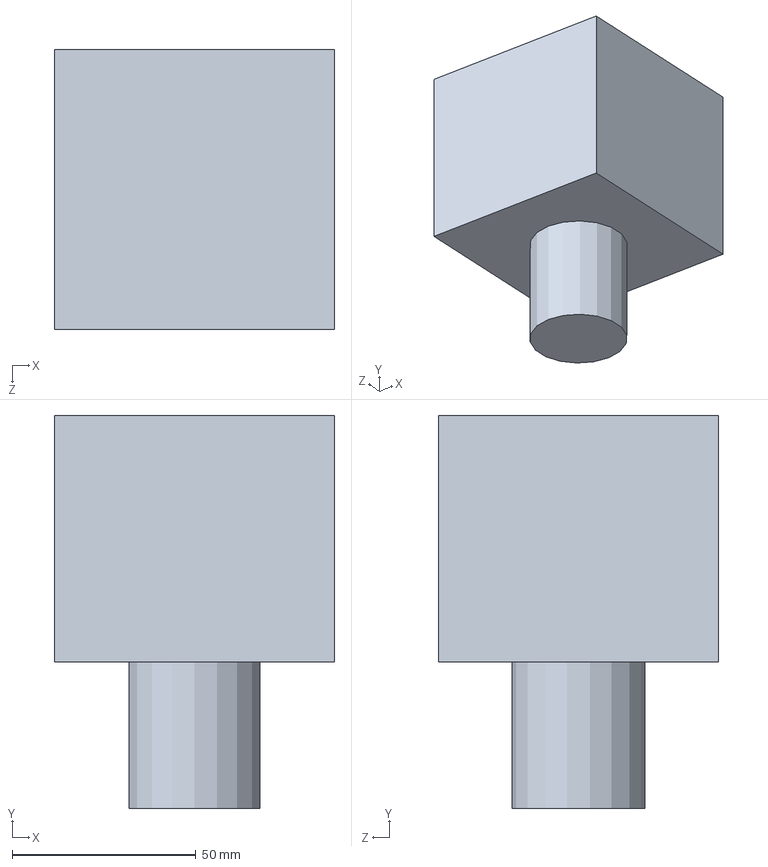
[picture p75: CAD file, 2020-12-12]
2D MOT/SAES Getter_D100-5/2D MOT Pump outer.SLDPRT
76.2 x 106.9 x 76.2 mm
