sbanik1/UHV-Chamber-Designs/2D MOT/Tenway Cross/OvenTube.SLDPRT

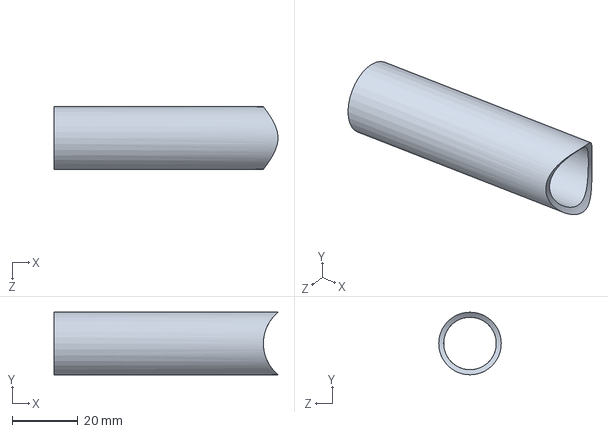
[picture p76: CAD file, 2020-12-12]
2D MOT/Tenway Cross/OvenTube.SLDPRT
68.2 x 19.1 x 19.1 mm
