sbanik1/UHV-Chamber-Designs/6 Way Cross Setup/6 Way Cross Getter SAES D-500/6WayPump inner.SLDPRT

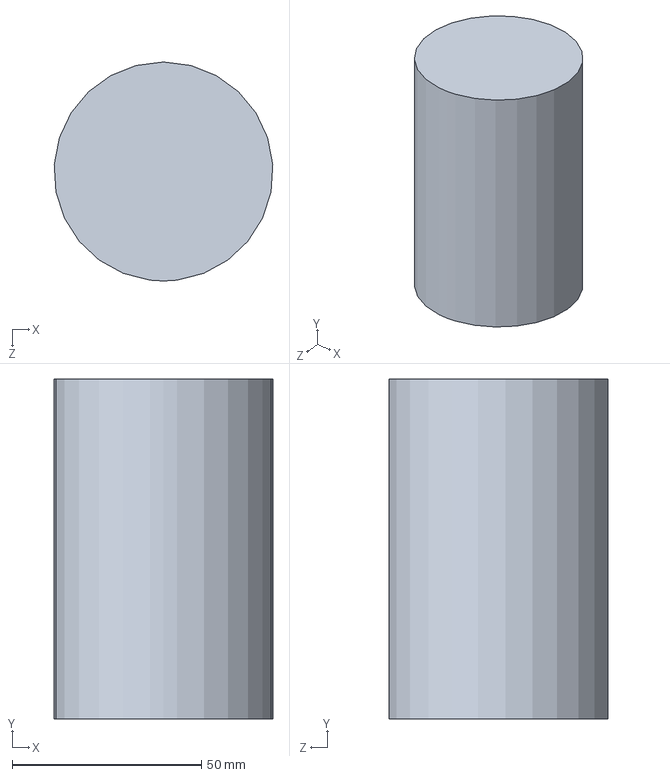
[picture p77: CAD file, 2020-12-12]
6 Way Cross Setup/6 Way Cross Getter SAES D-500/6WayPump inner.SLDPRT
57.8 x 89.9 x 57.9 mm
