sbanik1/UHV-Chamber-Designs/6 Way Cross Setup/Damped posts/Damped Post for 6 way cross P1.SLDPRT

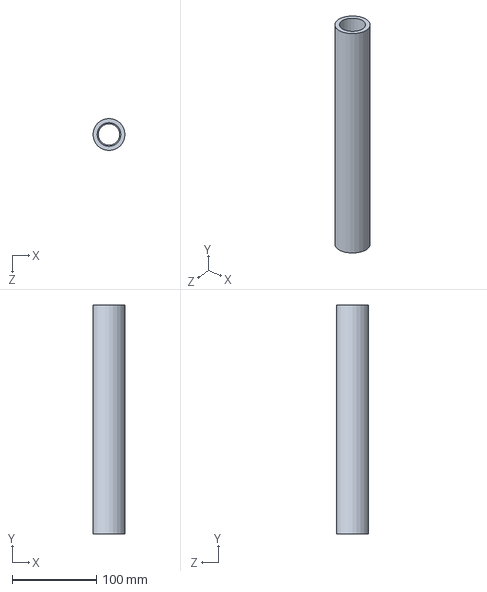
[picture p78: CAD file, 2020-12-12]
6 Way Cross Setup/Damped posts/Damped Post for 6 way cross P1.SLDPRT
38.1 x 272.1 x 38.1 mm
