sbanik1/UHV-Chamber-Designs/Bread Boards/Bread Board MOT side NO HOLES.SLDPRT

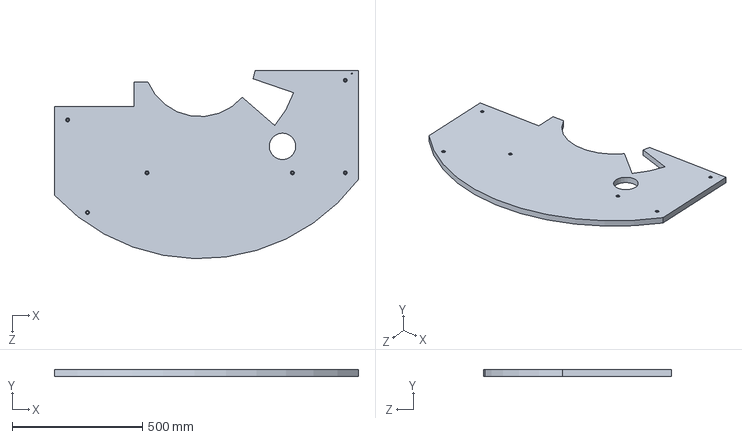
[picture p79: CAD file, 2020-12-12]
Bread Boards/Bread Board MOT side NO HOLES.SLDPRT
1168.4 x 25.4 x 723.6 mm
