sbanik1/UHV-Chamber-Designs/Main Chamber/Bucket Window/ISWindow.SLDPRT

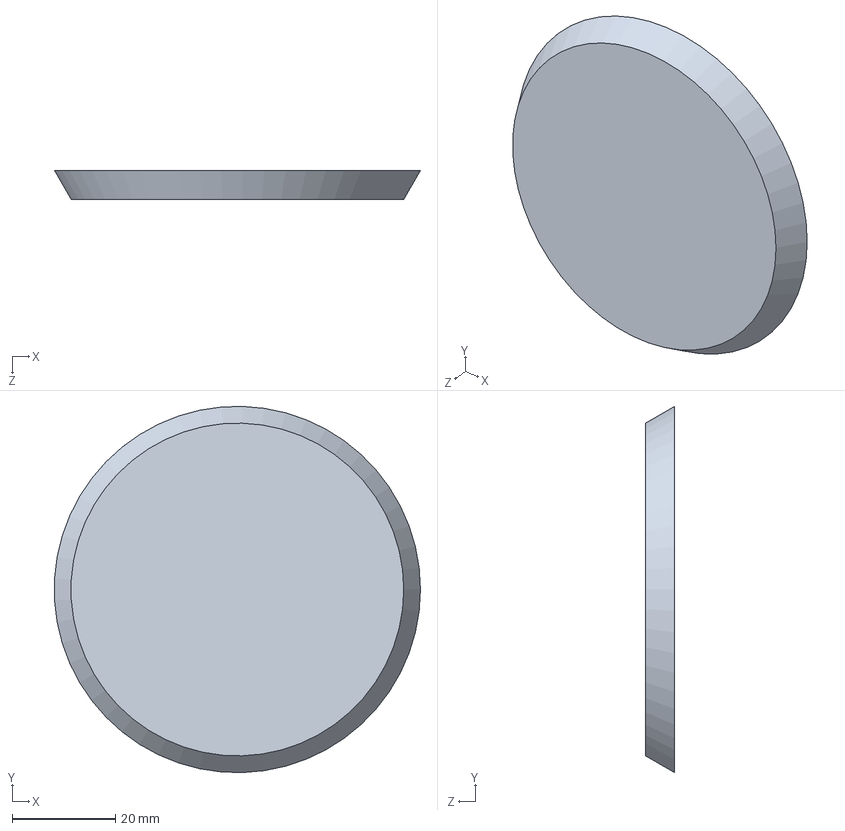
[picture p80: CAD file, 2020-12-12]
Main Chamber/Bucket Window/ISWindow.SLDPRT
70.9 x 71.0 x 5.63 mm
