sbanik1/UHV-Chamber-Designs/Bread Boards/Bread Board MOT side.SLDPRT

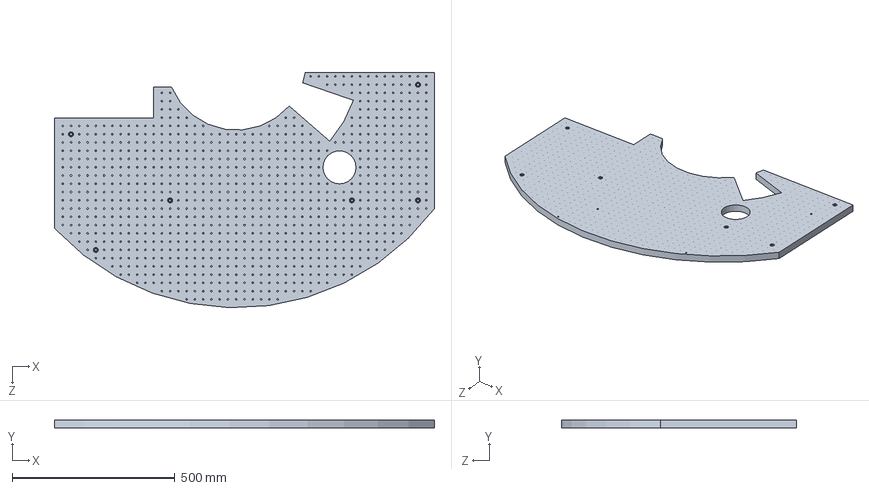
[picture p81: CAD file, 2020-12-12]
Bread Boards/Bread Board MOT side.SLDPRT
1168.4 x 25.4 x 723.6 mm
