sbanik1/UHV-Chamber-Designs/Main Chamber/Bucket Window/ISAdaptor.SLDPRT

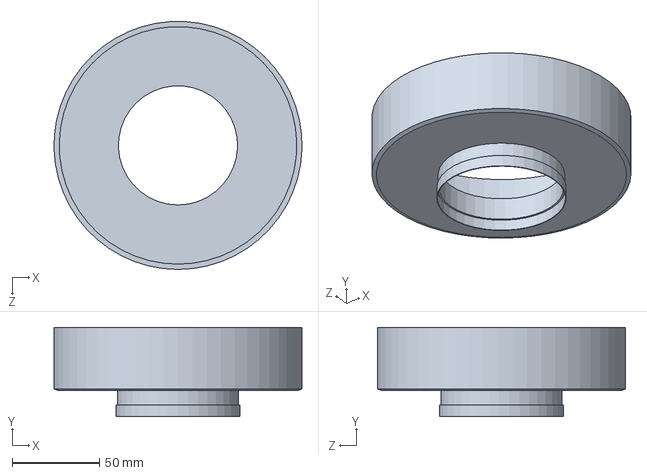
[picture p82: CAD file, 2020-12-12]
Main Chamber/Bucket Window/ISAdaptor.SLDPRT
142.2 x 51.1 x 142.1 mm
