sbanik1/UHV-Chamber-Designs/Bread Boards/Bread Board free side NO HOLES.SLDPRT

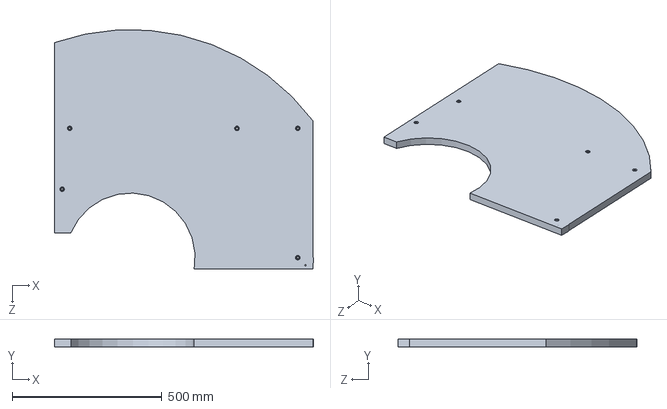
[picture p83: CAD file, 2020-12-12]
Bread Boards/Bread Board free side NO HOLES.SLDPRT
865.3 x 25.4 x 798.8 mm
