sbanik1/UHV-Chamber-Designs/2D MOT/Tenway Cross/CameraTube.SLDPRT

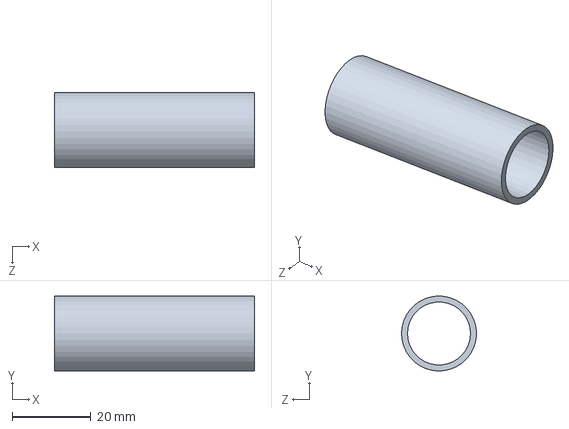
[picture p84: CAD file, 2020-12-12]
2D MOT/Tenway Cross/CameraTube.SLDPRT
50.8 x 19.0 x 19.1 mm
