sbanik1/UHV-Chamber-Designs/Main Chamber/2.75 VP Assembly/2.75 Window/2.75 Window P1-1.SLDPRT

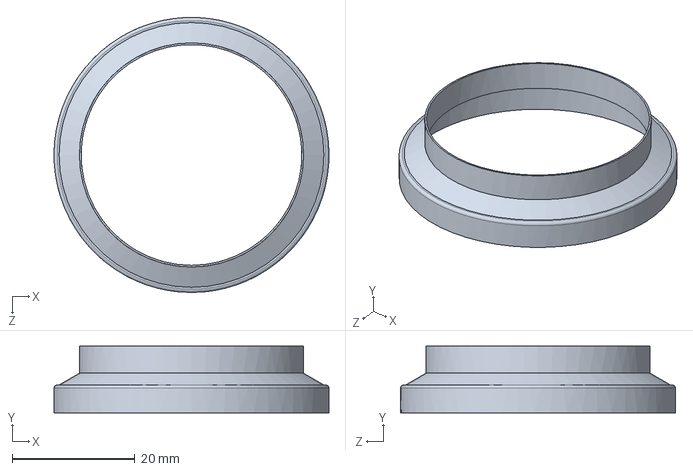
[picture p85: CAD file, 2020-12-12]
Main Chamber/2.75 VP Assembly/2.75 Window/2.75 Window P1-1.SLDPRT
44.9 x 10.9 x 44.9 mm
