sbanik1/UHV-Chamber-Designs/2D MOT/Tenway Cross/MiniFlange-weld-mine.SLDPRT

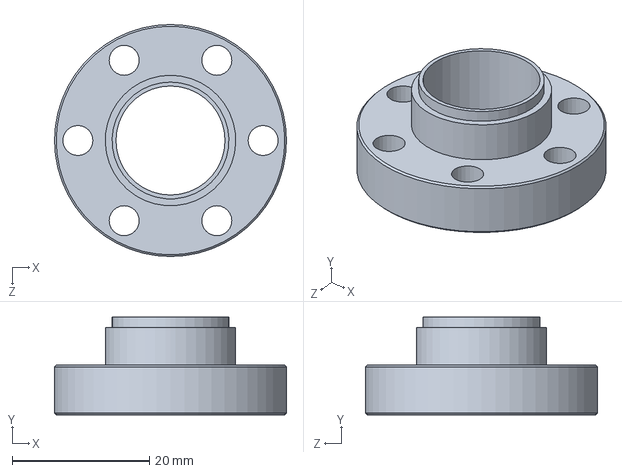
[picture p86: CAD file, 2020-12-12]
2D MOT/Tenway Cross/MiniFlange-weld-mine.SLDPRT
33.8 x 14.2 x 33.8 mm
