sbanik1/UHV-Chamber-Designs/2D MOT/Tenway Cross/ChamberTube.SLDPRT

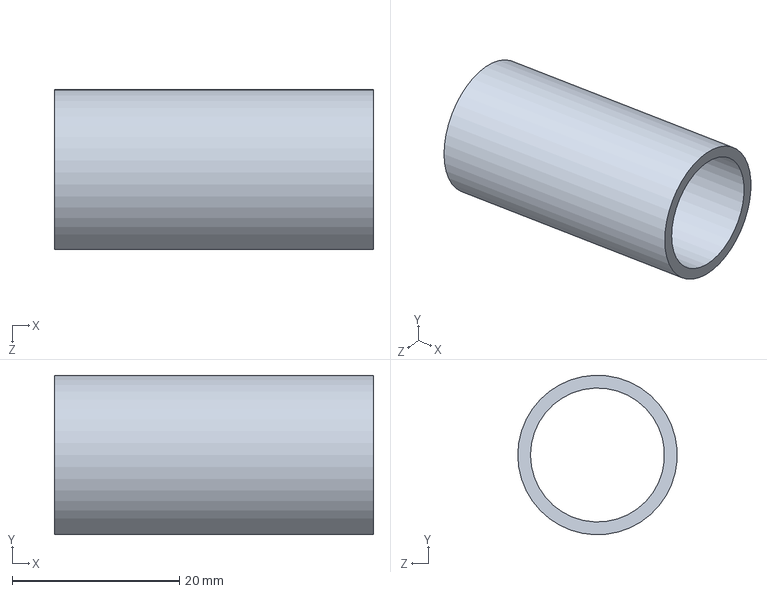
[picture p87: CAD file, 2020-12-12]
2D MOT/Tenway Cross/ChamberTube.SLDPRT
38.1 x 19.0 x 19.1 mm
