sbanik1/UHV-Chamber-Designs/2D MOT/Erbium Source/Er Source P1-1_110002.SLDPRT

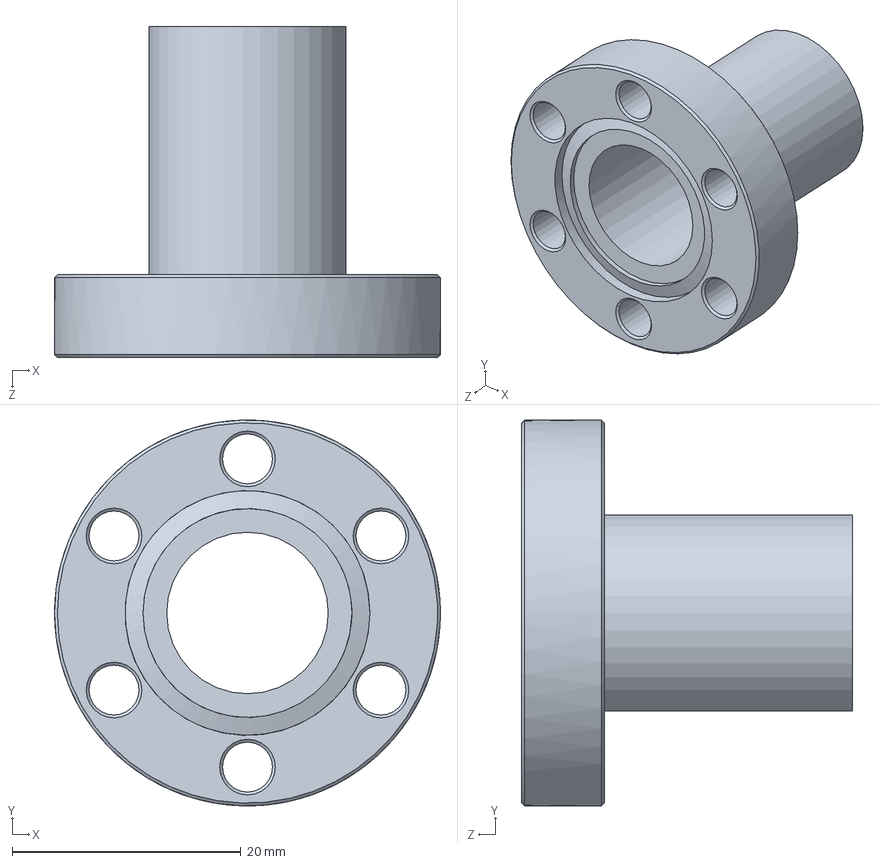
[picture p88: CAD file, 2020-12-12]
2D MOT/Erbium Source/Er Source P1-1_110002.SLDPRT
33.8 x 33.8 x 29.0 mm
