sbanik1/UHV-Chamber-Designs/2D MOT/Erbium Source/Er Source P2_fn-0275.SLDASM

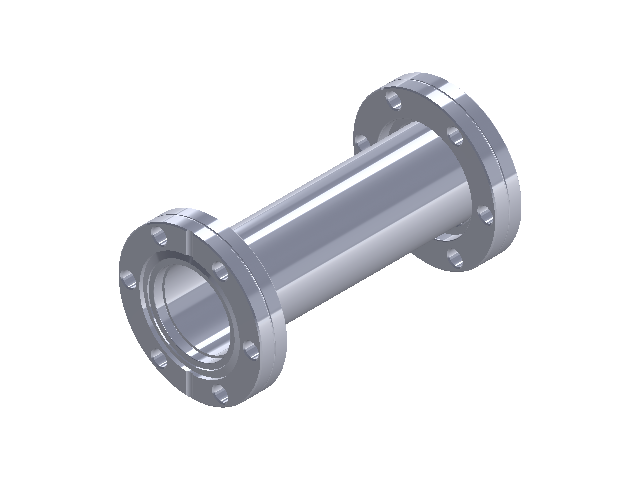
[picture p89: CAD file, 2020-12-12]
2D MOT/Erbium Source/Er Source P2_fn-0275.SLDASM
Er Source P2-2-2_P0001614
Er Source P2-2-1_P0000127
Er Source P2-1-2_P0000489
Er Source P2-1-1_P0000436
