sbanik1/UHV-Chamber-Designs/Main Chamber/VP distances/Main VP Distances.PDF

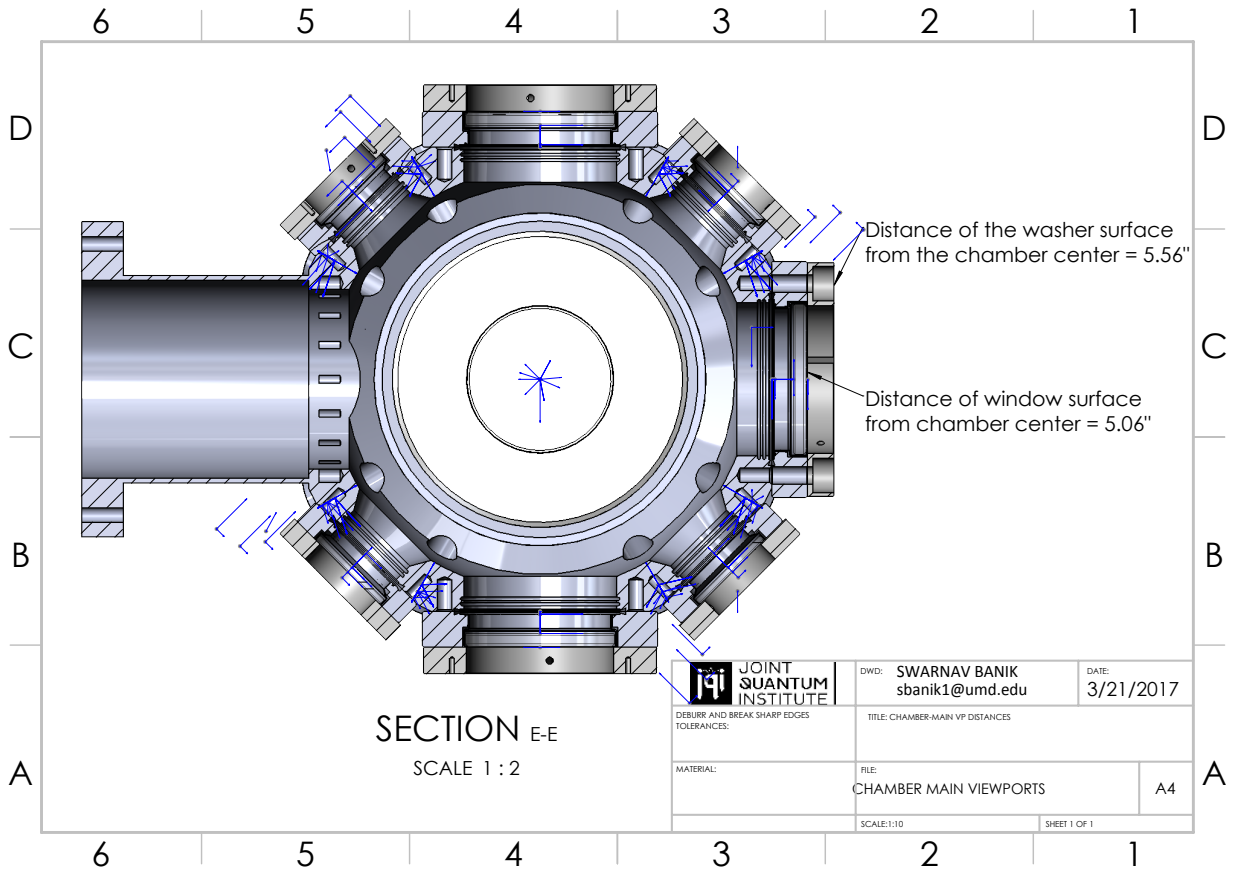
[picture p101: page 1]
SECTION E-E; SCALE 1 : 2

Distance of the washer surface
from the chamber center = 5.56"

Distance of window surface
from chamber center = 5.06"

SWARNAV BANIK DWD: sbanik1@umd.edu | DATE: 3/21/2017

DEBURR AND BREAK SHARP EDGES TOLERANCES: | TITLE: CHAMBER-MAIN VP DISTANCES

MATERIAL: CHAMBER MAIN VIEWPORTS | FILE: | A4

SCALE:1:10 | SHEET 1 OF 1
