sbanik1/UHV-Chamber-Designs/Main Chamber/VP distances/Mini VP Distances.PDF

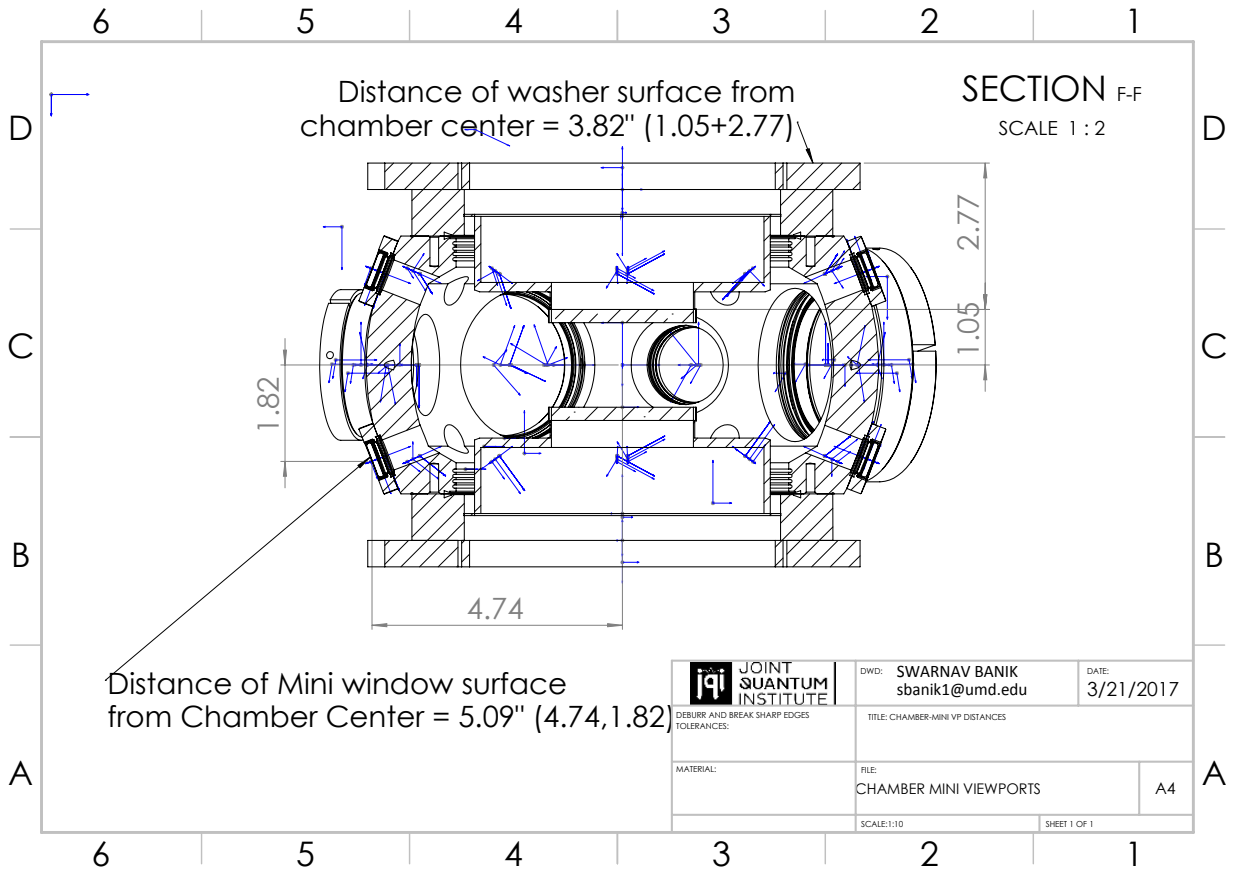
[picture p102: page 1]
SECTION F-F; SCALE 1 : 2

Distance of washer surface from
chamber center = 3.82" (1.05+2.77)

Distance of Mini window surface
from Chamber Center = 5.09" (4.74,1.82)

SWARNAV BANIK DWD: sbanik1@umd.edu | DATE: 3/21/2017

DEBURR AND BREAK SHARP EDGES TOLERANCES: | TITLE: CHAMBER-MINI VP DISTANCES

MATERIAL: | FILE: CHAMBER MINI VIEWPORTS | A4

SCALE:1:10 | SHEET 1 OF 1
